nakujaproject/Internship-2026/03_RECOVERY/Weekly_Memo/Recovery Week 2 Report .pdf

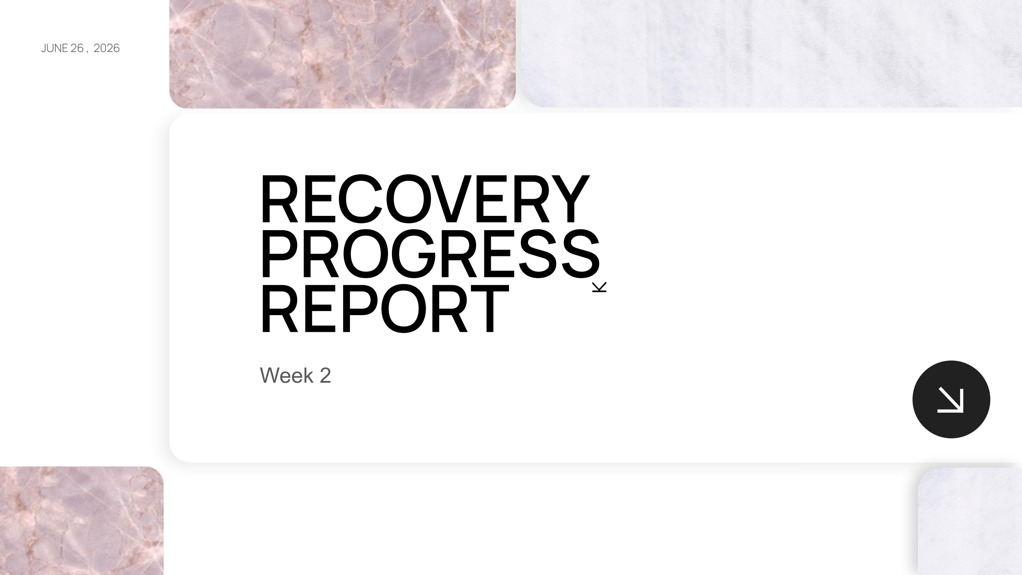
[picture p94: page 1]

K

# RECOVERY PROGRESS REPORT

## Week 2

JUNE 26 , 2026

# This Week’s Tasks

## - - XBEE Antenna Research - - General purchases and beginning of X-BEE importation process - -Free RTOS Configuration Review - - 3D printing Shear Pins - - Implement circuit changes for dual memory storage - - Documentation - - Code cleaning - - cooking crimson powder

# Extracting data from the flash memory

## 1. Fixing the flash memory erase

The initial software attempted to clear the SPI flash memory using a standard byte-overwrite method. This was ineffective because NOR flash hardware strictly requires a dedicated sector-erase command to reset memory bits and prevent data corruption.

## 2. Reading the data correctly

The recovery program was trying to read complex binary code from a file named 'flight', while the flight computer was actually saving simple plain text into a file named 'data'.

The flight computer was saving the telemetry data as simple, plain text . But the recovery program was trying to read it as complex binary code. Because of that mismatch, the recovered data just looked like gibberish.

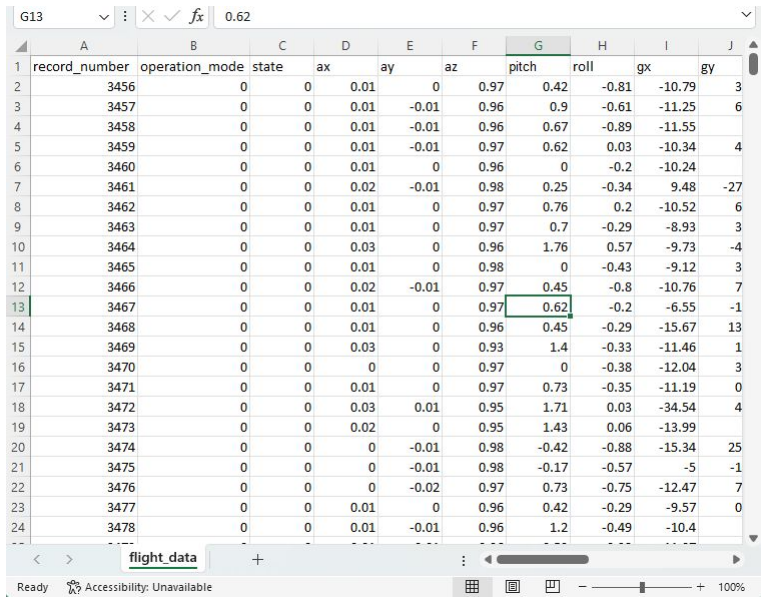
[picture p95: figure]

## 1. Successfully extracted the sensor data from the Flight Computer (FC) 2. Validation will be conducted accordingly 3. GPS not connected - TBD

# Updated the base station schematic and designed the PCB

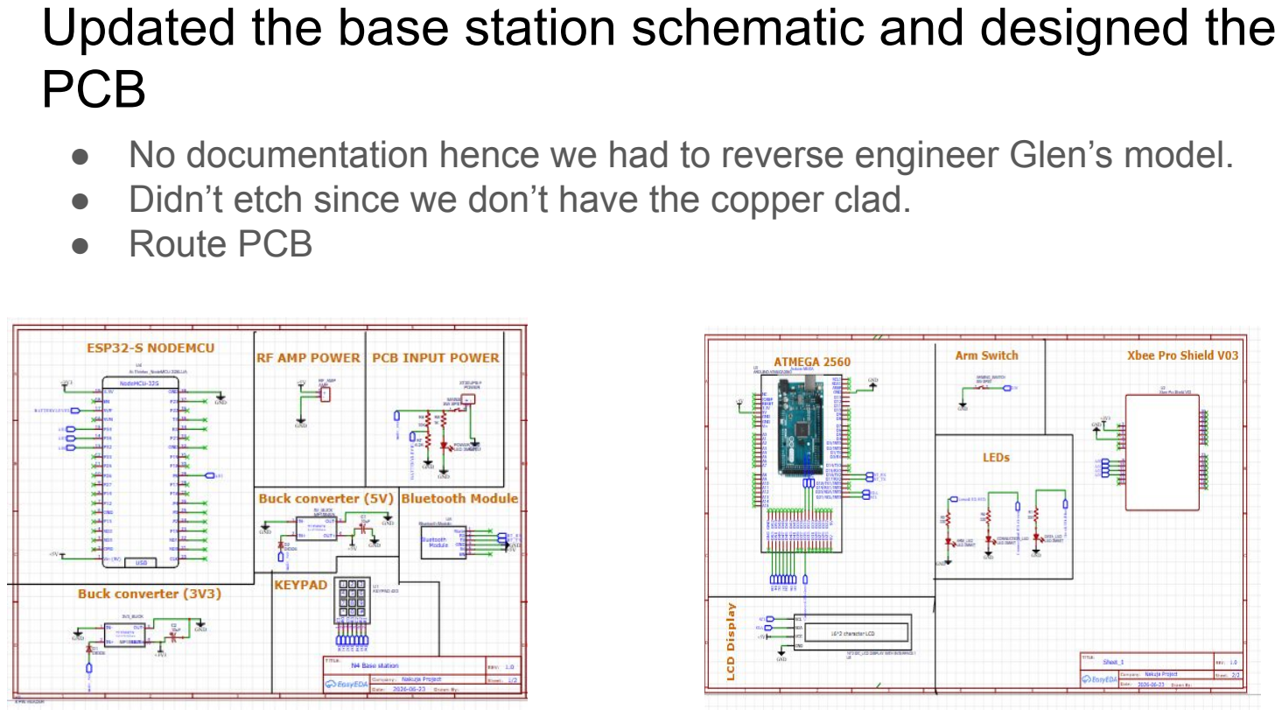
[picture p96: page 5]

- No documentation hence we had to reverse engineer Glen’s model.
- Didn’t etch since we don’t have the copper clad.

## - Route PCB

# Routed PCB

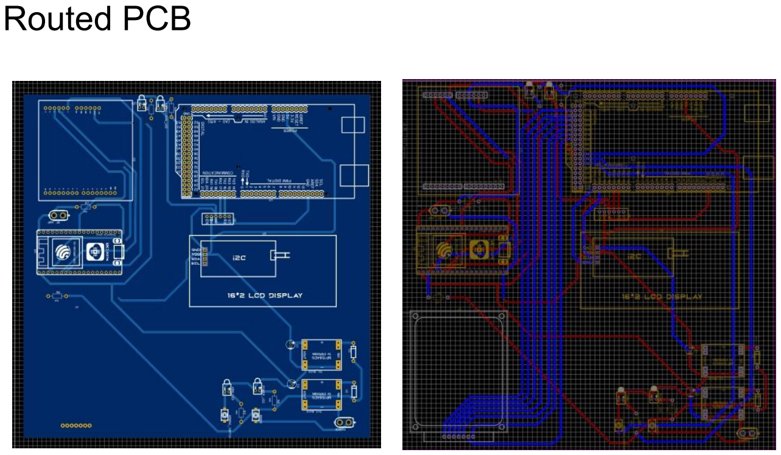
[picture p97: page 6]

# Designed Battery Holder for Base Station

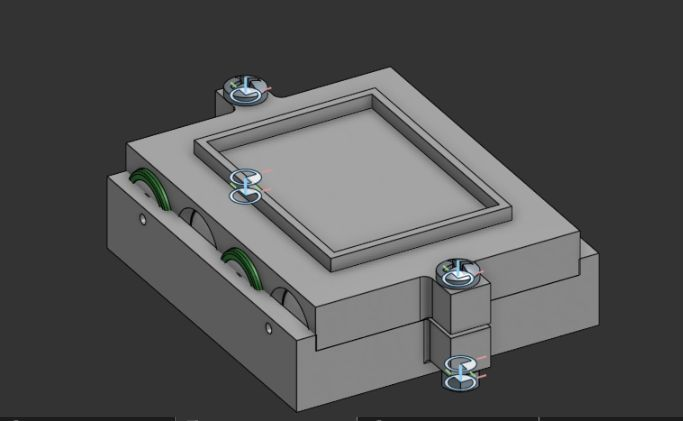
[picture p98: figure]

Is yet to be 3D printed.

# Code Review and Cleaning

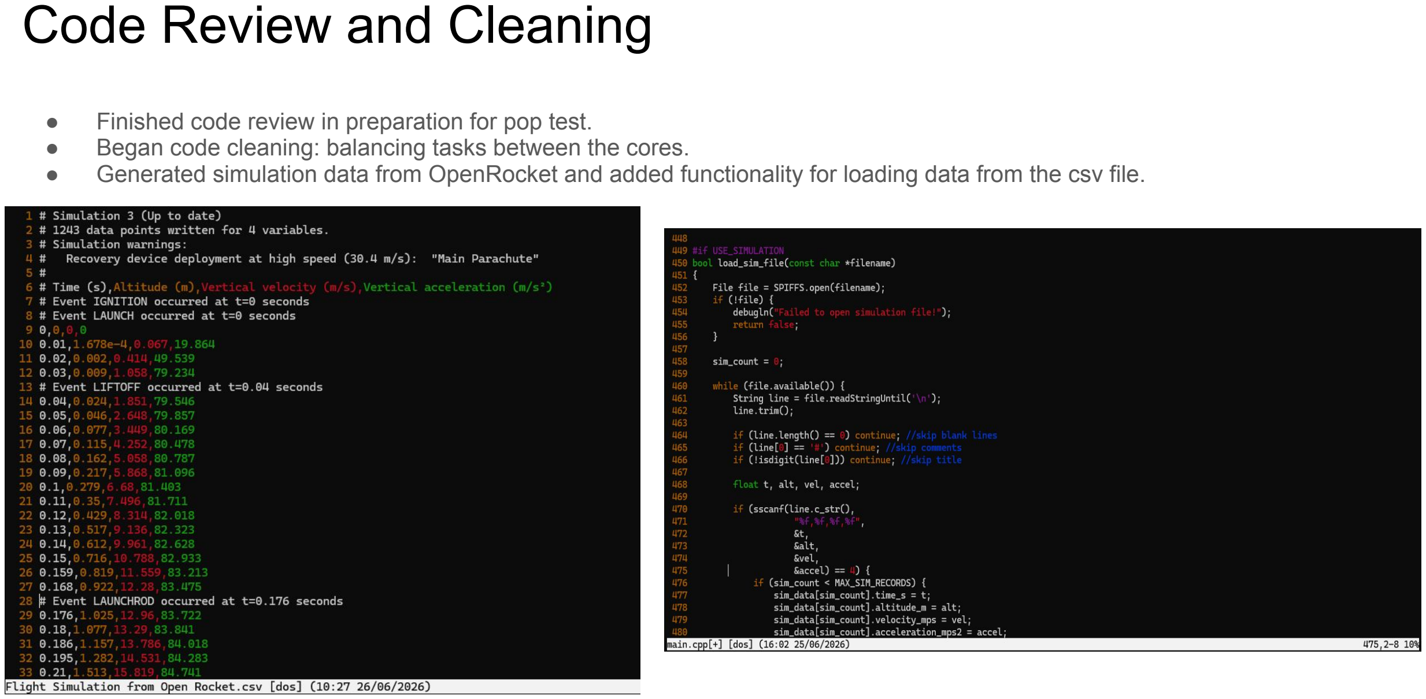
[picture p99: page 8]

- Finished code review in preparation for pop test.
- Began code cleaning: balancing tasks between the cores.
- Generated simulation data from OpenRocket and added functionality for loading data from the csv file.

# Dockerized the Base Station

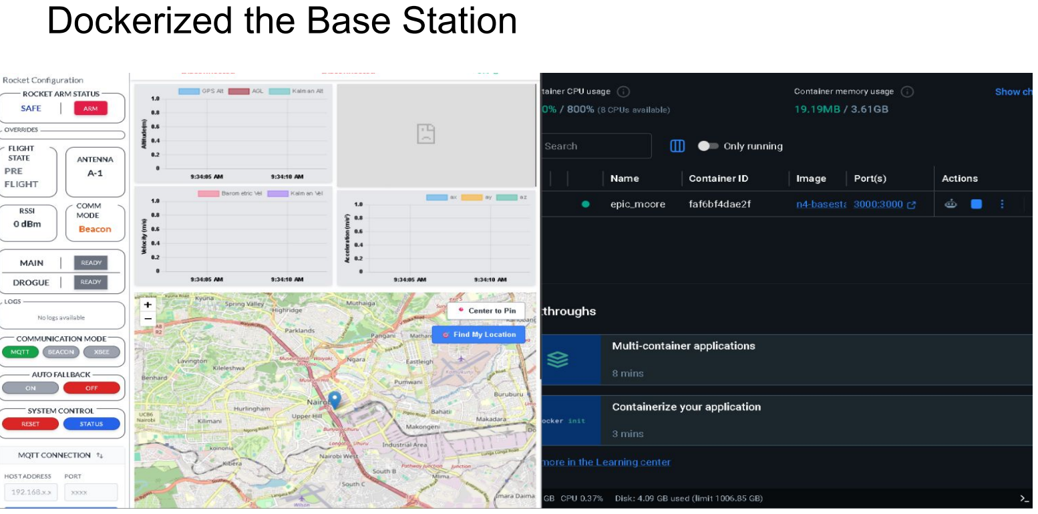
[picture p100: page 9]

# Use of COTS altimeter as backup

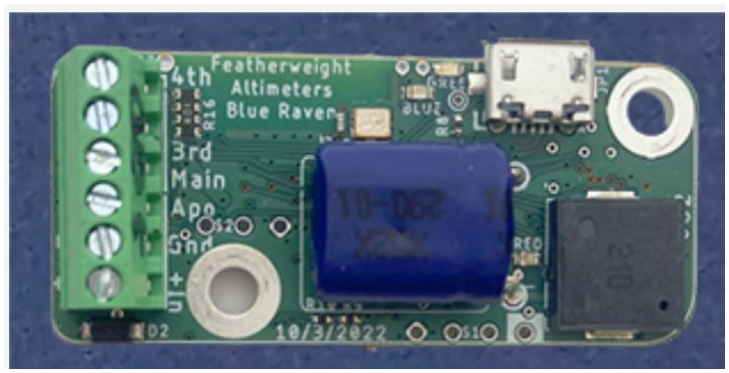
[picture p101: figure]

### https://www.apogeerockets.com/Electronics-Payloads/Dual-Deploy ment/Blue-Raven-Altimeter

# Next weeks tasks

- Etch Base-Station PCB - Pop test - 3D - Printing shear pins ,Battery Holder, explosion caps - Kalman Filter Testing - Make circuit changes for dual memory storage - Verification of parachute design to ensure they are able to handle the new motor etc - Changes to base-station Arduino MEGA code - Extending parachute suspension lines
