nakujaproject/Internship-2026/03_RECOVERY/Weekly_Memo/RECOVERY PROGRESS REPORT WEEK 1.pdf

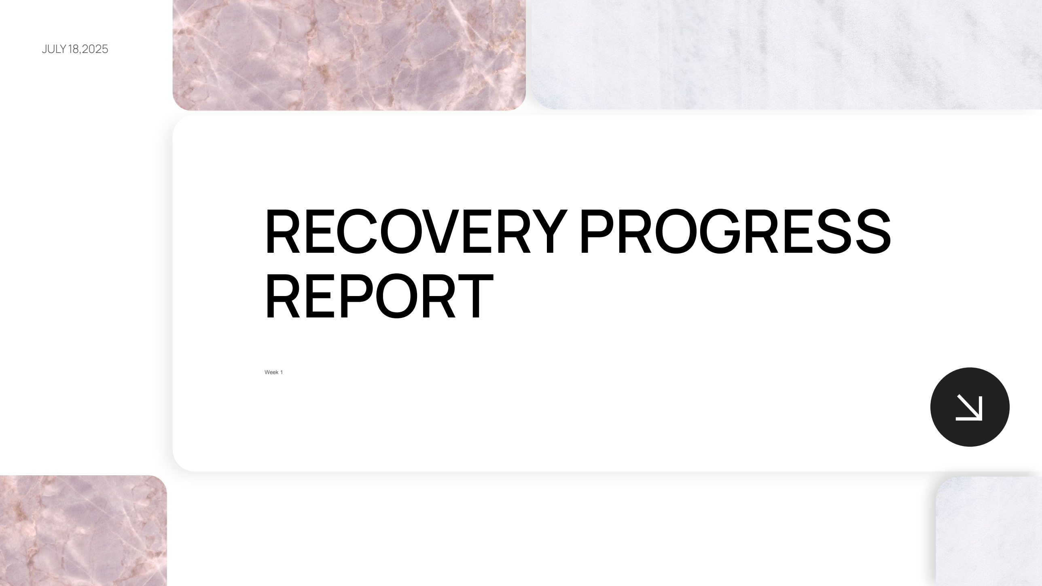
[picture p102: page 1]

# RECOVERY PROGRESS REPORT

Week 1

JULY 18,2025

# This Week’s Tasks

Define tasks for 12 weeks and develop mind map for doing them Set up base-station on every PC
Connect Base Station to Flight Computer
Brief on Parachute System by Mwaura based on his project Brief by Glenn based on his project
Explanation of Kalman Filter Implementation
Inventory

## Defining the 12 weeks tasks and Developing a Mind Map

Github Projects

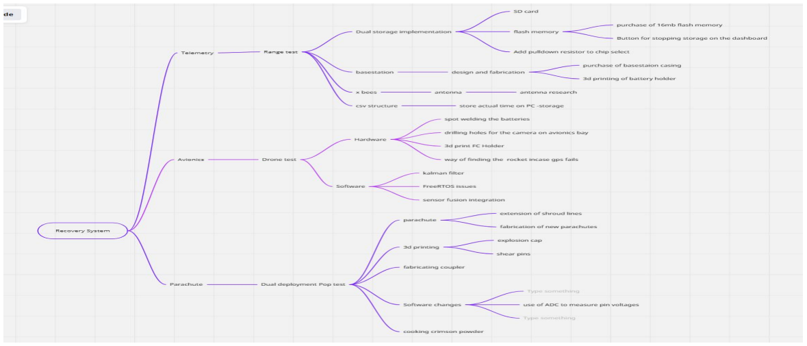
[picture p103: figure]

## Setting Up Base Station on Every PC

Changes made for cross platform compatibility

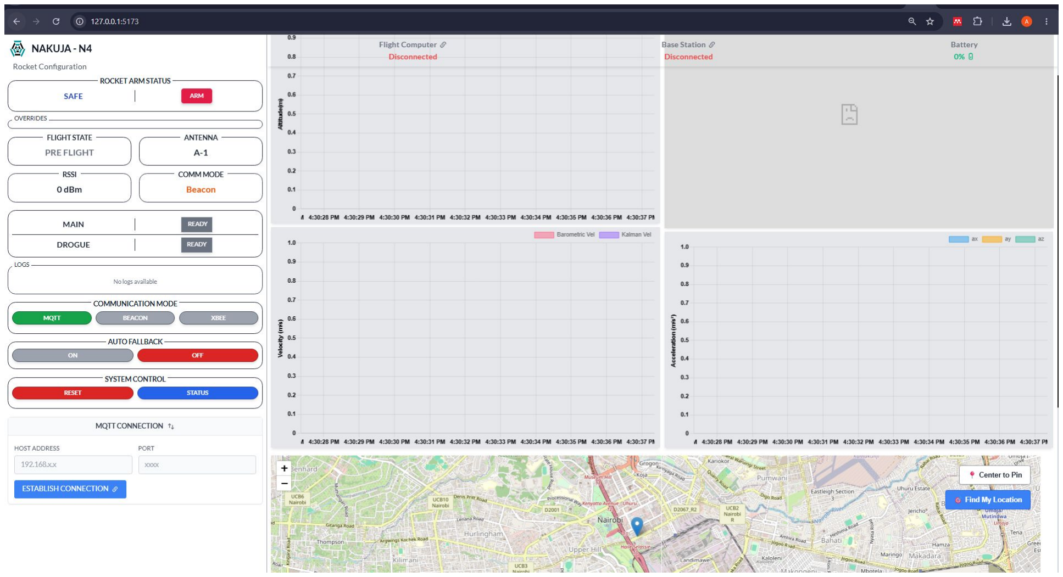
[picture p104: figure]

## Pop Test DRY RUN

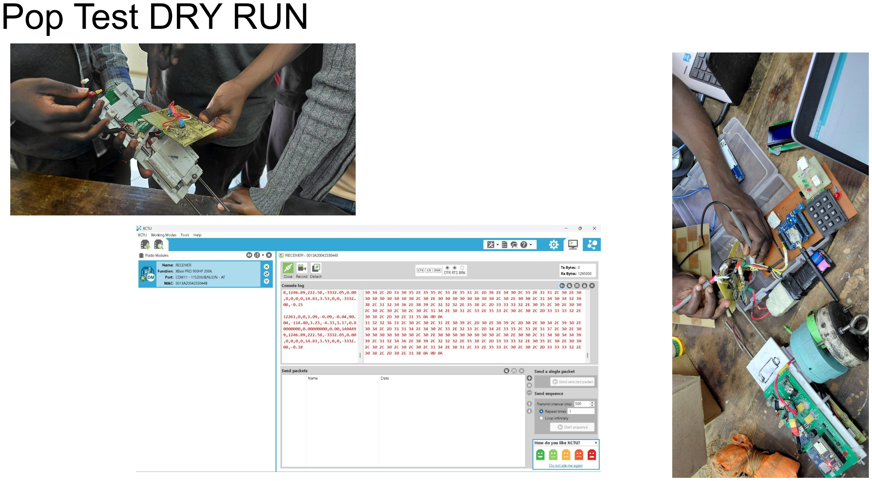
[picture p105: page 5]

# Next Week’s task

- XBEE Antenna Research
- General purchases and beginning of X-BEE importation process
- Machining Coupler
-Free RTOS Configuration Review
- 3D printing Shear Pins
- Research on the effects of pressure changes in the avionics bay during flight
- Implement circuit changes for dual memory storage
- Documentation
- Code cleaning
