nakujaproject/Internship-2026/02_AIRFRAME/Weekly_Memo/Airframe week two progress report.pdf

# Airframe team

Week two Progress Report

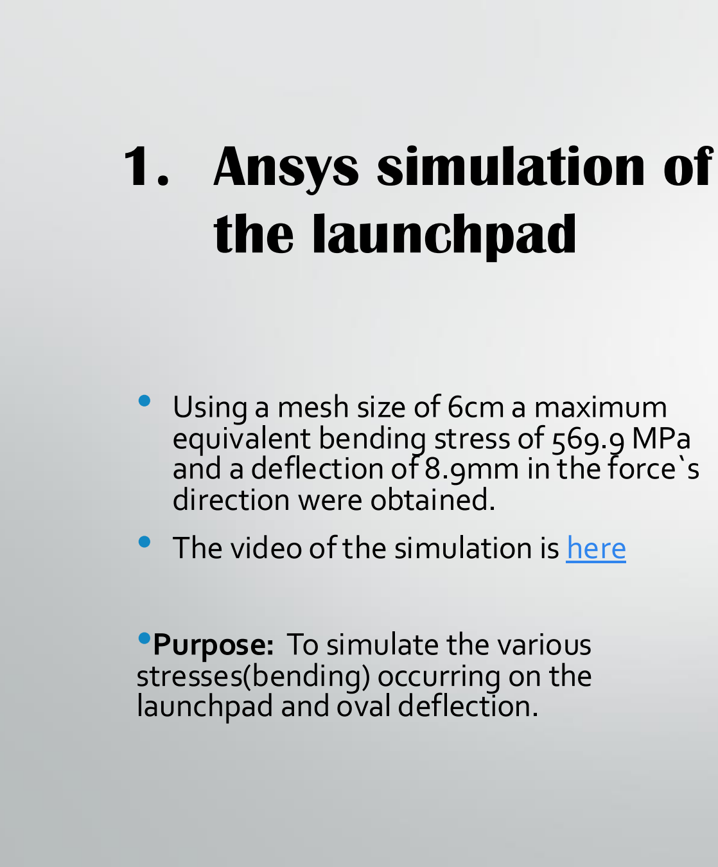
[picture p106: figure]
1. Ansys simulation of the launchpad; • Using a mesh size of 6cm a maximum equivalent bending stress of 569.9 MPa; direction were obtained. • The video of the simulation is here; •Purpose: To simulate the various stresses(bending) occurring on the launchpad and oval deflection.
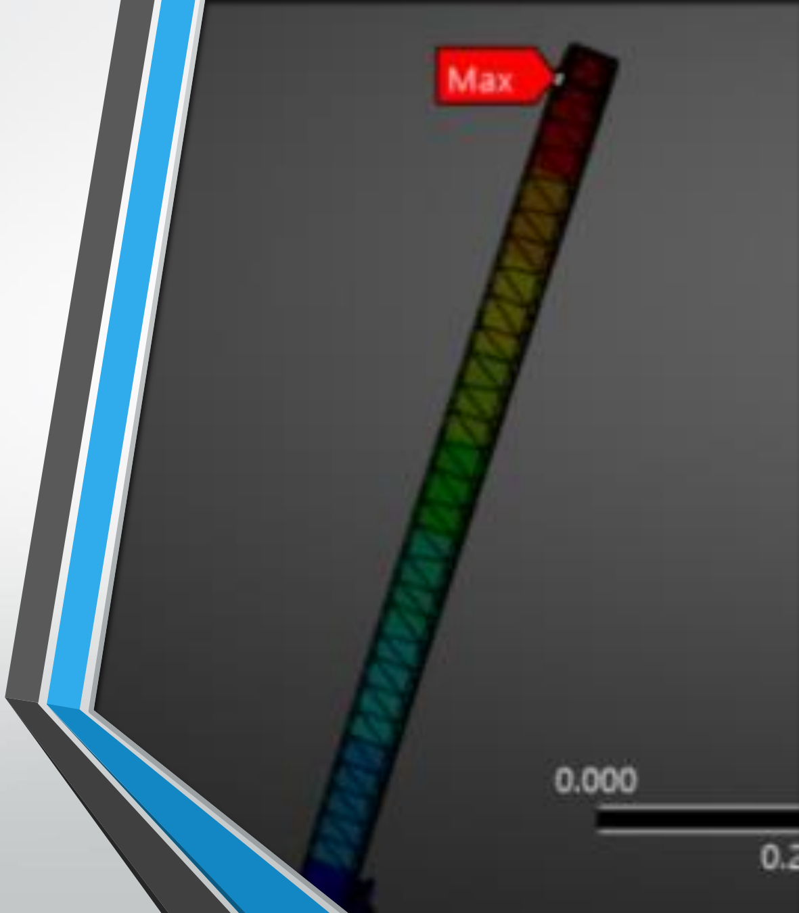
[picture p107: figure]

and a deflection of 8.9mm in the force`s

## 2.Mesh independence study of the launchpad

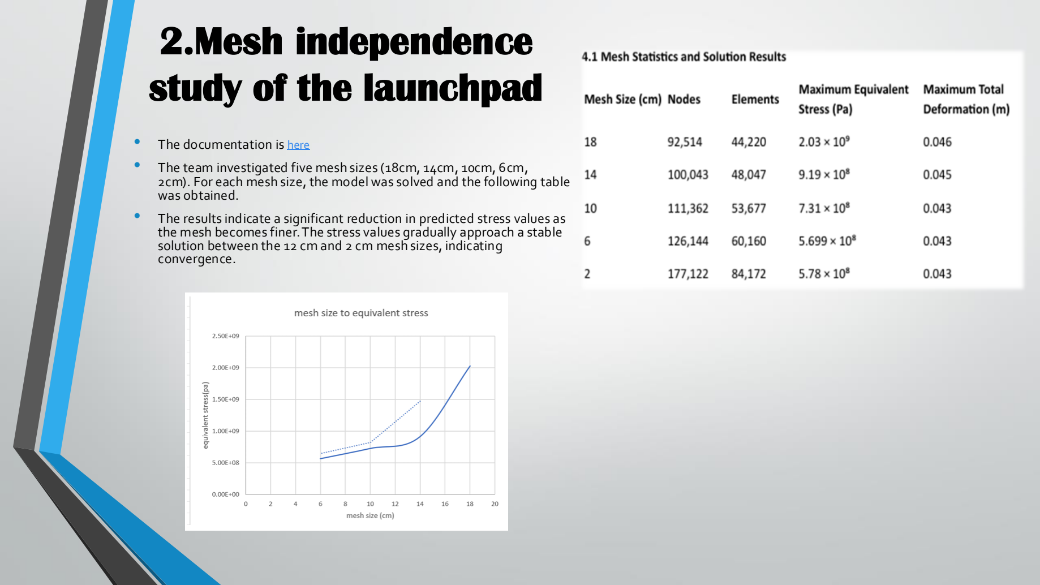
[picture p108: page 3]

- The documentation is here (https://discord.com/channels/1062703976711209010/1062705386697801828/1519920103523618966)
- The team investigated five mesh sizes (18cm, 14cm, 10cm, 6cm, 2cm). For each mesh size, the model was solved and the following table was obtained.
- The results indicate a significant reduction in predicted stress values as the mesh becomes finer. The stress values gradually approach a stable solution between the 12 cm and 2 cm mesh sizes, indicating convergence.

- For deformation, the results remain nearly constant throughout the refinement process, demonstrating that deformation predictions are largely insensitive to further mesh refinement beyond the 6 cm mesh.

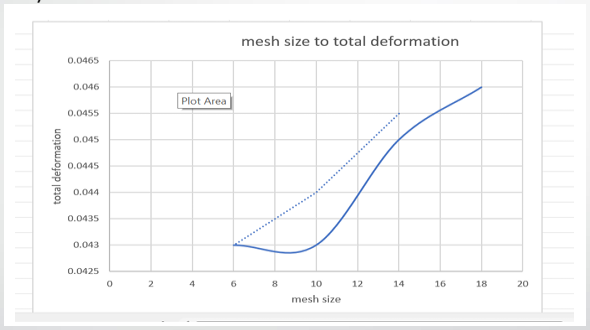
[picture p109: figure]

- Based on the convergence behavior observed during mesh refinement, the 6 cm mesh was selected for all subsequent analyses s because it provides accurate results while minimizing computational requirements.

## 3. Theoretical calculations of stress(

bending and axial), deflection,

## buckling analysis and safety of factor

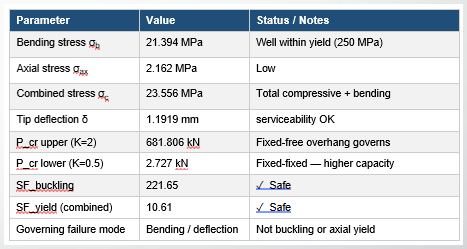
[picture p110: figure]

- The team embarked on the theoretical analysis of the launchpad to verify the ansys simulations.
- The documentation is here (https://discord.com/channels/1062703976711209010/1062705386697801828/1519937529242058773) and the following results were obtained:
- The deflection obtained is almost similar to the ansys simulation (0.78 of the simulation). The stresses can`t be directly compared as he theoretical is directional while the simulation is equivalent.

## 4. Airframe Tasks preparation and listing

- The team was also able to prepare a mindmap of all the tasks that
need to be undertaken here (https://app.xmind.com/share/8dNVX2TA?xid=Qb3cZIfH)

## 5. Challenges experienced

- Lack of internet connection.
- Lack of access to workshops for fabrication.
- Computational resources required for Ansys.

Next week tasks
- Launchpad finishes: reaming, painting etc

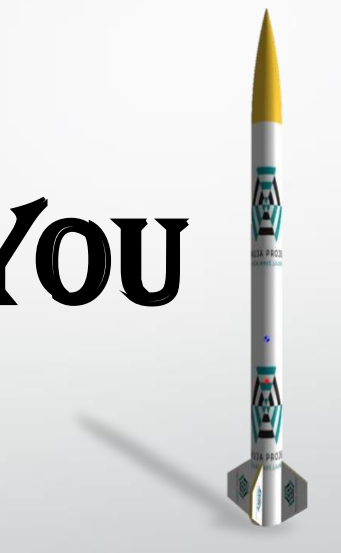
[picture p111: figure]

# Thank you
