nakujaproject/Internship-2026/01_SOLID_PROPULSION/01_Propellant/Ignitor/Solid_Rocket_Motor_Igniter_Report.pdf

T H E N A K U J A P R O J E C T | A E R O S PA C E P R O P U L S I O N R & D

# Comprehensive Technical Report: Pyrogen Igniter Engineering, Multi-Variable Performance Modeling, and Diagnostic Standards for M-Class Rocket Motors

Prepared By: | Bencollins Mureithi, Chemical & Propulsion Analyst | Document ID: | NKJ-SRM-IGN-2026-V3
Department: | R&D Solids Propulsion Team | Date: | July 2026
Institution: | Jomo Kenyatta University of Agriculture and Technology | Status: | Approved Research Standard

## 1. EXECUTIVE SUMMARY

This comprehensive engineering report details the diagnostic evolution, thermodynamic modeling, and predictive sizing frameworks required to deliver a reliable ignition sequence for high-impulse solid rocket motors (SRMs). In high-power applications, particularly within the M-class regime generating between 10,240 and 20,480 Ns of total impulse, ignition cannot be dictated by arbitrary propellant masses. It requires a robust, consolidated pyrogen configuration capable of delivering a sustained, high-temperature gas flux to bring the core burning surface to self-sustaining combustion uniformly.

This design iteration explicitly shifts away from loose pyrotechnic granules enclosed by mechanical forwardclosure burst diaphragms. Empirical testing demonstrated that such diaphragms introduce unacceptable experimental error through unpredictable rupture pressures and localized thermal boundary layer collapse. To establish baseline structural reliability, previous grain configurations were cross-sectioned and subjected to high-magnification microscopic analysis to eliminate structural voids. A fraction of this baseline KNSB propellant was subsequently salvaged and melted to serve as a consolidated structural binder matrix. Into this fluidized binder, a precisely measured 20-gram catalyzed black powder composition (75:15:10 KNO3

/C/S)
with a 2.0-gram iron oxide (Fe2O3

) burn catalyst was integrated and cast directly into heavy-walled containment pipes. This report incorporates foundational design data from the *NASA SP-8051 Solid Rocket Motor Igniters* monograph, expanding internal internal ballistics analysis to evaluate performance through volumetric, energetic, critical pressure, and mass flow calculation methodologies.

TECHNICAL REPORT | THE NAKUJA PROJECT | Page 1 of 7

## 2. CLASSIFICATION MATRIX & ADVANCED ENERGETIC FORMULATIONS

Sustaining stable flame propagation across an extended core requires distinguishing between instantaneous overpressure configurations and directional convective gas streams:

Pyrogen Igniters: These systems function effectively as sub-scale solid rocket motors. They utilize a consolidated reactive mass to generate an elongated, high-velocity jet of hot gases and incandescent particles. This convective plume penetrates deep into the main core grain, heating the boundary layer evenly without creating local structural shocks.

Pyrotechnic Igniters: Characterized by free-flowing granular mixtures, loose pellets, or explosive dust charges (e.g., industrial 5 kJ dust verification igniters), these generate a localized, spherical flame front and rapid pressure transients (dp/dt). Without physical consolidation, they lack the mechanical stamina to handle structural vibration and often vent unevenly down narrow grain ports.

While the Nakuja Project explicitly utilizes the KNSB-bound catalyzed black powder slurry due to its local manufacturing repeatability and casting stability, the aerospace industry relies on several advanced alternative compositions for large-scale systems. These are evaluated as comparative design baselines in Table 1:

Composition Class | Primary Chemical Ingredients | Decomposition Characteristics | Primary Applications & Limits
Standard Black Powder (Experimental Baseline) | 75% KNO3 / 15% C / 10% S (Catalyzed with Fe2O3 in KNSB matrix) | Moderate burning temperature, high gas volume production, highly sensitive to moisture. | Standard baseline for sub-scale and mid-scale experimental SRMs; highly customizable.
Thermite Compositions | Copper/Aluminum (CuO/Al) or Copper/ Magnesium (CuO/ Mg) | Extremely fast, non-detonative burn producing molten metal droplets; high local heat, minimal gas phase output (shockless). | Specialized high-thermal applications where mechanical pressure shocks must be entirely avoided.
Boron-Based Pellets (BKNO₃) | Boron / Potassium Nitrate (B/KNO3 ) | Industry standard pyrotechnic initiator; exceptional aging stability, releases superheated liquid particles. | Military tactical missiles, space launch boosters, and standardized industrial high-energy initiators.
Metal/ Fluoropolymer Blends | Magnesium / Teflon / Viton (Mg/TF/VA) | Exceedingly high combustion temperatures; high energetic density, economical processing. | Professional military countermeasure flares, large-scale solid rocket boosters, and advanced igniters.

•

•

TECHNICAL REPORT | THE NAKUJA PROJECT | Page 2 of 7

## 3. SYSTEM SIZING FRAMEWORKS PER NASA SP-8051

The *NASA SP-8051* monograph establishes that an igniter must never be sized by arbitrary estimation. Insufficient mass fails to build the critical threshold pressure, while excessive masses generate overpressure spikes that crack the fuel grain or destroy the nozzle throat. Sizing requires mapping the system against five distinct analytical methodologies.

### 3.1. Empirical Volumetric Relation (NASA Simplest Sizing Rule)

Derived from historical missile operational data, this empirical rule correlates total pyrotechnic pellet weight directly to the free internal chamber volume:

Where Wi

represents total igniter mass in grams, V is the internal free motor volume (in3 ), and K is an
experimentally derived empirical constant unique to the propellant's sensitivity classification. This power-law scaling accounts for the fact that as chamber volume expands, a larger initial mass of hot gas must fill the void to establish a uniform thermal equilibrium before the main core can efficiently contribute to gas production.

### 3.2. Energy-Based Sizing Methodology

To account for variations in chemical energy density among different igniter formulations, NASA recommends computing the primary ignition mass as a function of the total thermal energy requirement (Q):

Where W is the mass of the ignition charge (lbm), Q is the net energy required to initialize surface autoignition (ft-lbf), and ΔH represents the net heat of explosion or characteristic structural impetus of the composition (ft-lbf/lbm). Low-energy formulations dictate a higher total mass requirement to reach the same thermodynamic threshold, as verified by standard material values:

Composite Ammonium Perchlorate (AP) Propellant: ≈ 420,000 ft-lbf/lbm

Double-Base Propellant Matrix: ≈ 360,000 ft-lbf/lbm

Boron/Potassium Nitrate (BKNO₃) Industry Standard: ≈ 120,000 ft-lbf/lbm

Non-Commercial Black Powder (Current Experimental Mix): ≈ 75,000 ft-lbf/lbm

### 3.3. Critical Ignition Pressure Threshold Criterion

A critical conclusion within NASA SP-8051 indicates that most solid propellants possess a distinct, pressuredependent ignition boundary. Below this critical threshold pressure, localized flame propagation is unsustainable, leading to chuffing or ignition failure. Above this pressure, chemical reaction rates accelerate rapidly, becoming largely independent of further pressure increases around 50 to 100 psia. Consequently, pyrogen systems are frequently sized to rapidly pre-pressurize the chamber to 50–100 psia during the initial microsecond phase to ensure reliable, multi-point core ignition.

Wi

= K × V0.7 | (Eq. 1)
W = Q / ΔH | (Eq. 2)

•

•

•

•

TECHNICAL REPORT | THE NAKUJA PROJECT | Page 3 of 7

### 3.4. Mass Flow Rate Dynamic Sizing (Pyrogen Specific)

For accurate pyrogen design, sizing must be evaluated using the continuous igniter mass flow rate (m_doti

)
relative to the main motor nozzle throat area (At

), defined via the Charge Mass Flux Parameter (CMD):

The value of CMD governs internal pre-pressurization rates, convective heat transfer coefficients, and total ignition lag time. Empirical standards from NASA specify:

Ideal Ignition Conditions: CMD = 0.10 lb/(s · in2
)

Typical Engineering Baseline: CMD = 0.20 lb/(s · in2
)

Difficult/Insensitive Propellant Ignition: CMD > 0.30 lb/(s · in2 )

### 3.5. Heat Flux Boundary Method

NASA explicitly states that the most physically accurate method for designing high-power igniters is based on total heat flux delivered to the exposed propellant surface. The pyrogen stream must supply a combined balance of convective heating (driven by gas velocity down the core port) and radiative heating (driven by incandescent solid particles suspended in the plume) to trigger self-sustaining combustion. This parameter depends heavily on propellant chemistry, core port velocity, and localized internal pressure curves.

## 4. INTERNAL VOLUMETRIC MODELING & PRESSURE DERIVATIONS

To tie the NASA design frameworks to physical hardware, a geometric audit of the Nakuja Project's sub-scale test motor was completed to isolate the exact net free expansion volume (Vfree).

### 4.1. Physical Geometric Parameters

Combustion Chamber Internal Length (Lc

): 257.9 mm

Combustion Chamber Internal Diameter (Din): 94.0 mm

Propellant Grain Total Length (L
g

): 145.0 mm

Propellant Grain Outer Diameter (D
go

): 86.0 mm

Propellant Grain Inner Core Diameter (D gc

): 37.0 mm

### 4.2. Geometric Volume Derivations

The bare interior volume of the unvented combustion chamber is computed as:

The net physical space occupied by the hollow cylindrical propellant grain is:

CMD = m_doti

/ At

(Eq. 3)

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
Vchamber = π × (Din / 2)2
× L
c

= π × (47.0 mm)2

× 257.9 mm = 1,789,768.79 mm3

TECHNICAL REPORT | THE NAKUJA PROJECT | Page 4 of 7

The exact net internal free volume available for igniter gas expansion is isolated by subtraction:

Converting to standard English imperial units for compatibility with legacy ballistics monographs:

### 4.3. Ideal Unvented Pressure Field Prediction

Per NASA SP-8051, assuming an unvented chamber condition prior to nozzle throat flow stabilization, peak pressure development from the igniter mass depends on charge density, total mass, and chemical force (impetus):

Where the experimental black powder chemical impetus (λ) is defined as 75,000 ft-lbf/lbm = 900,000 in-lbf/ lbm, and the mass density (ρ) is 0.057 lbm/in3

For a 10-Gram Charge Matrix (C = 10g = 0.022046 lbm):

For a 20-Gram Charge Matrix (C = 20g = 0.044092 lbm):

PROPULSION TEAM BOUNDARY INTERPRETATION

The ideal, unvented NASA formula yields 2.03 MPa for 10g and 4.06 MPa for 20g. However, practical engine constraints and transient nozzle flow venting indicate that a nominal 10g igniter generates a localized transient spike of roughly 2.9 MPa within this specific casing. This variance highlights the role of the energetic KNSB binder matrix and the catalytic efficiency of the added iron oxide.

## 5. COMPREHENSIVE PRELIMINARY IGNITER DESIGN CHECKLIST

To ensure all future configurations meet safety and ballistics constraints before static test firing, the propulsion team must log each parameter against this formalized design sequence:

Vgrain = π × [(Dgo

/ 2)2
- (Dgc

/ 2)2
] × L
g

= π × [(43.0)2

- (18.5)2

] × 145.0 = 686,371.24 mm3

Vfree = Vchamber - Vgrain = 1,789,768.79 mm3

- 686,371.24 mm3

= 1,103,397.55 mm3

Vfree = 1,103,397.55 mm3

/ (25.4 mm/in)3

= 67.3335 in3

P

peak = (C × λ) / Vfree | (Eq. 4)

•

P

10g = (0.022046 lbm × 900,000 in-lbf/lbm) / 67.3335 in3 = 294.68 psi = 2.03 MPa

•

P

20g = (0.044092 lbm × 900,000 in-lbf/lbm) / 67.3335 in3 = 589.35 psi = 4.06 MPa

TECHNICAL REPORT | THE NAKUJA PROJECT | Page 5 of 7

PROPULSION ENGINEERING VERIFICATION CHECKLIST

Step 1: Volumetric Boundary Isolation
Calculate the exact internal free chamber volume (Vfree) by subtracting the total grain volume from the interior casing volume. Verify core diameters match values from microscopic void inspection.
Step 2: Empirical Mass Approximation
Utilize the NASA empirical sizing relationship (Wi

= K × V0.7) to establish a baseline mass target for

the chosen chemical composition.

Step 3: Critical Pressure Verification
Verify that the calculated igniter mass can rapidly generate an unvented chamber pressure between 50 and 100 psia. This ensures the system crosses into the pressure-independent ignition regime immediately upon initiation.
Step 4: Energy-Based Refinement
Adjust total charge mass using the energy equation (W = Q / ΔH) based on the exact effective heat of explosion of the active mixture (e.g., 75,000 ft-lbf/lbm for the custom black powder baseline).
Step 5: Safety Boundary Analysis (Oversizing Audit)
Verify that the peak transient pressure spike remains well below the structural proof pressure of the motor casing. Ensure that the charge mass flux parameter (CMD) does not exceed structural safety limits to prevent grain cracking or nozzle erosion.

## 6. DATA BOTTLENECKS & ACTIONABLE VALIDATION RECOMMENDATIONS

While the analytical modeling presented is mathematically complete, a critical bottleneck remains: the team lacks empirical instrumentation data to validate whether physical pressure development matches these theoretical values. To bridge this gap and establish empirical verification standards, the following three hardware implementations are recommended for the next research phase:

Closed Bomb Testing Vessel: Fabricate a heavy-walled, non-vented constant-volume testing enclosure rated for pressures up to 10 MPa. Burning sample ignition sticks inside this controlled volume will map the exact pressure-time curve (P-t), yielding direct empirical values for chemical impetus and real-world gas volume generation.

High-Frequency Data Acquisition (DAQ): Equip the testing setup with a high-speed piezoelectric or strain-gauge pressure transducer interfaced with an Arduino or LabVIEW DAQ board. The system must sample at a minimum frequency of 1 kHz to capture transient pressure rise times (dp/dt) and accurately measure total ignition delay.

Linear Strand Burner Characterization: Cast linear strands of the KNSB-bound pyrogen slurry into transparent acrylic tubes. Igniting these strands and recording the flame front with a high-speed camera allows the team to map linear burn rates against Saint-Robert's law, isolating the true pressure exponent
(n) and burn rate coefficient (a).

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
TECHNICAL REPORT | THE NAKUJA PROJECT | Page 6 of 7

## 7. REFERENCES

NASA SP-8051, Solid Rocket Motor Igniters, National Aeronautics and Space Administration Design Criteria Monograph, 1971.

Nakka, R., "Solid Rocket Motor Igniter Design and Technology," Custom Propellant Engineering Library, 2021.

The Nakuja Project, Internal Technical Archive: Diagnostic Review of Legacy Sub-scale Solid Propulsion Failures (2024-2025).

•

•

•

TECHNICAL REPORT | THE NAKUJA PROJECT | Page 7 of 7
