nakujaproject/Internship-2026/01_SOLID_PROPULSION/01_Propellant/Grains/Technical_Report_On_Mitigation_Of_Pressure_Spikes.pdf

## TECHNICAL REPORT: MITIGATION OF UNPREDICTABLE PRESSURE SPIKES IN BATES

Prepared by: Bencollins Mureithi Team: The Nakuja Project
June 16, 2026

### 1. Introducon

- Background:

Experimental rocketry requires high ballisc consistency for safety and performance. The BATES (Ballisc Test and Evaluaon System) grain geometry is specifically engineered to provide a neutral, stable thrust profile through a maintained burning surface area. However, praconers oen observe errac, non-neutral pressure-me curves characterized by sudden spikes and deviaons from simulaon. These phenomena indicate that the propellant is not burning according to its geometric design.
- Objecves:

This research aims to address these performance instabilies by ensuring grain structural integrity and achieving predictable combuson kinecs through the opmizaon of the propellant matrix and ignion systems.

### 2. Technical Discussion

The transion from errac pressure spikes to predictable combuson requires managing both the physical state of the grain and the dynamics of the ignion process.

### 2.1 Rheological and Structural Integrity

The formaon of voids and micro-cracks is the primary driver of unpredicted pressure surges.
- Surfactant Integraon: Molten sorbitol exhibits high surface tension, which can hinder the weng of KNO3 parcles and lead to air entrapment. The addion of surfactants, such as Sodium Laureth Sulfate (SLES) or Lecithin, serves to reduce this interfacial tension. This promotes a homogeneous, void-free slurry that ensures the grain burns uniformly without localized hot spots.

- Plascizaon: Sorbitol inherently forms a brile, crystalline matrix that is suscepble to thermal shock and mechanical fracture. Incorporang plascizers like glycerol introduces flexibility into the binder, allowing the grain to resist crack propagaon under operang pressures. By maintaining a crack-free structure, the propellant preserves its intended burning surface area.

### 2.2 Combuson Kinecs and Ignion

Controlling the burn rate involves moderang both the thermal output and the chemical iniaon.
- O/F Rao and Parcle Size: Shiing the Oxidizer-to-Fuel rao from the standard 65:35 toward a 60:40 or 58:42 composion increases the fuel-rich binder content, which acts as a thermal heat sink to moderate peak combuson temperatures. Simultaneously, using coarser KNO3 parcles prolongs the melng phase, resulng in a more controlled, gradual release of oxygen.
- Ignion Reliability: Delayed ignion contributes to non-uniform pressure rises. Implemenng a two-part ignion system—consisng of a high-sensivity primer and an internal pyrogen charge—ensures that the enre grain surface iniates combuson simultaneously, prevenng the localized pressure surges associated with slow or uneven ignion.

### 3. Ignion System Design: Raonale and Diagnosc Criteria

The propulsion system employs a two-part ignion sequence consisng of an iniator (igniter) and a surface-applied propellant primer. This configuraon is crical for achieving reliable, synchronized ignion across the grain surface and migang the risks associated with transient ignion delays.

### 3.1 Necessity of the Two-Part System

The requirement for a dual-stage system arises from the physical and chemical properes of the solid propellant grain, which oen possesses high auto-ignion temperatures or geometries that challenge uniform flame propagaon.
- Sensivity Bridging: The primer serves as an intermediary layer with high sensivity to thermal flux. The igniter provides the inial high-energy output required to trigger the primer, which in turn acts as a high-intensity catalyst to force the main propellant grain into self-sustaining combuson.
- Simultaneous Flame Propagaon: Reliance on a single igniter can result in localized ignion, leading to uneven burning or combuson instabilies. The primer ensures the flame front spreads instantaneously across the enre exposed propellant surface area, facilitang a rapid and controlled pressure rise to design levels.
- Migaon of Hang-Fire: The system design proacvely prevents "hang-fire" scenarios— where ignion is delayed beyond the specified me window—by ensuring that energy transmission is uniform and effecve across the combuson chamber.

### 3.3 Diagnosc Idenficaon of Delayed Ignion

Indicator | Characterisc Behaviour | Interpretaon
P-t Slope | A disnct "step" or "plateau" in the pressure curve immediately following the acvaon signal | Indicates a lag between the inial igniter discharge and the onset of stable grain combuson.
Ignion Interval | Time duraon from the electrical acvaon signal (t0) to the achievement of 10% of maximum chamber pressure (Pmax). | Exceeding the design-specified threshold for this interval constutes a confirmed ignion delay.
Acousc/Vibraon Data | Sharp, irregular pressure spikes or "chuffing" sounds | Suggests non-uniform flame propagaon or the accumulaon of gases before sudden, violent ignion of the grain.

Monitoring these parameters ensures that the transion from inial ignion to steady-state interior balliscs remains within established safety and performance envelopes.

### 4. Conclusion

The errac ballisc performance observed in BATES-configured KNSB motors is largely a result of structural defects and inconsistent iniaon dynamics. By focusing on grain structural integrity—specifically through the use of surfactants to eliminate voids and plascizers to prevent fractures—and refining combuson kinecs via O/F rao adjustments and improved ignion, the motor's actual chamber pressure can be aligned with simulated design predicons

### 5. References

- Nakka, R. (n.d.). "KN-Sorbitol Propellant." Richard Nakka's Experimental Rocketry Web Site.
- European Conference for Aeronaucs and Space Sciences (EUCASS). (2019). "Laser Ignion and Combuson Study of KNO3-Sorbitol based Solid Propellant".
- Technical Report: "Surfactants & Plascizers for KNSB Solid Propellant" (The Nakuja Project, 2026).
