nakujaproject/Internship-2026/01_SOLID_PROPULSION/01_Propellant/Ignitor/Comprehensive_Nichrome_Igniter_Analysis.pdf

T H E N A K U J A P R O J E C T | A E R O S PA C E P R O P U L S I O N R & D

# Comprehensive Technical Report: Mathematical Modeling and Sizing Constraints of Nichrome 80 Conductor Elements for Pyrogen Systems

Prepared By: | Bencollins Mureithi, Chemical & Propulsion Analyst | Document ID: | NKJ-PROP-EE-2026-V2
Department: | R&D Solids Propulsion Team | Date: | July 2026
Academic Inst: | Jomo Kenyatta University (JKUAT) | Technical Focus: | Electro-Thermal Sizing & Resistance Optimization

## 1. DOCUMENT SCOPE AND ELECTRO-THERMAL OBJECTIVES

This comprehensive technical document delivers a thorough electro-thermal analysis required to optimize fine Nichrome 80 resistance bridge wires (30 AWG and 32 AWG) for the reliable, remote initiation of custom KNSB-bound pyrogen configurations. In a consolidated pyrogen igniter, the bridge wire serves as the primary thermal transducer. Passing an electric current through this wire converts electrical energy into heat via Joule heating. To achieve immediate initiation of the primary composition (which incorporates elemental sulfur with an auto-ignition threshold of approximately 232°C), the bridge wire should ideally flash to a target temperature of 1000°C (1273.15 K). This extreme over-temperature guarantees immediate, multi-point ignition, eliminating ignition delay and preventing transient chuffing inside the motor casing.

Sizing the bridge wire requires solving the direct mathematical interdependencies between wire gauge, linear resistance, geometric length, source voltage, current drawdown, and thermal response times. This analysis isolates these parameters to provide actionable length, topology, and power recommendations for field-ready battery profiles.

## 2. FOUNDATIONAL MATHEMATICAL GOVERNING EQUATIONS

The electrical and thermodynamic performance of a fine uninsulated wire suspended inside a chemical matrix is governed by Ohm's Law, Joule's First Law, and the fundamental heat equation.

### 2.1. Physical Resistance Modeling

The initial electrical resistance (R) of a round conductor at room temperature depends on its geometric length and cross-sectional area:

R = ρ
e
× (L / A) = ρlinear × L | (Eq. 1)
TECHNICAL REPORT | THE NAKUJA PROJECT | Page 1 of 7

Where L is the active physical length of the wire segment (m), A is the cross-sectional area (π d2 / 4, m

2
), and ρ
e
is the material electrical resistivity. For premium Nichrome 80 (comprising 80% Nickel and 20% Chromium), ρ e
≈ 1.09 × 10-6 Ω·m at room temperature.

### 2.2. Joule Heating and Power Dissipation

When a constant DC voltage source (V) is applied across the isolated bridge wire, the electric current (I) drawn through the circuit is defined by Ohm's Law:

The instantaneous thermal power (P) dissipated as radiant heat across the conductor is defined by Joule's Law:

Equation 3 reveals a critical relationship for design optimization: under constant-voltage conditions, the thermal power output varies inversely with resistance. Shortening the wire decreases its resistance, which exponentially increases the current draw and the total power dissipation.

### 2.3. Thermodynamic Heat Accumulation

To model the transient temperature rise time (t

rise) before full ignition, we evaluate the system as a closed thermodynamic model. Neglecting small localized conductive losses into the surrounding slurry during the initial millisecond phase, the net energy (E) required to elevate the physical wire mass (m) from ambient temperature (Tambient = 20°C) to the target ignition threshold (Ttarget = 1000°C) is expressed as:

Where c
p

is the specific heat capacity of Nichrome 80 (450 J/(kg·K)), ΔT is the net temperature change (1000°C -20°C = 980°C), and m is isolated via the material mass density (ρm

= 8310 kg/m3
) multiplied by wire volume:

The required activation time (t

rise) to achieve immediate thermal breakdown is defined by the ratio of total energy to instantaneous power dissipation:

## 3. COMPREHENSIVE SIZING MATRICES FOR CONDUCTOR PROFILES

The physical and electrical baselines for standard Nichrome 80 wire gauges are defined as:

### 30 AWG Wire: Diameter d = 0.254 mm | Linear Resistance ρ

linear = 21.33 Ω/m

### 32 AWG Wire: Diameter d = 0.203 mm | Linear Resistance ρ

linear = 33.46 Ω/m

I = V / R | (Eq. 2)

P = I²

× R = V²
/ R | (Eq. 3)

E = m × c
p
× ΔT | (Eq. 4)

m = ρm

× A × L | (Eq. 5)

t

rise = E / P = (m × c
p

× ΔT) / (V²
/ R) | (Eq. 6)

•

•

TECHNICAL REPORT | THE NAKUJA PROJECT | Page 2 of 7

3.1. 30 AWG Parametric Performance Table
Length (mm) | Resistance (Ω) | Wire Mass (mg) | Energy to 1000°C (J) | Source Voltage (V) | Current Draw (A) | Power Output (W) | Time to 1000°C (ms)
5.0 mm | 0.1066 | 2.11 | 0.9285 | 3.7 V (1S Li-Ion) | 34.69 A | 128.36 W | 7.23 ms
| | | | 7.4 V (2S Li-Po) | 69.39 A | 513.46 W | 1.81 ms
| | | | 12.0 V (Lead-Acid) | 112.52 A | 1350.21 W | 0.69 ms
| | | | 24.0 V (Bench DAQ) | 225.04 A | 5400.84 W | 0.17 ms
10.0 mm | 0.2133 | 4.21 | 1.8569 | 3.7 V (1S Li-Ion) | 17.35 A | 64.18 W | 28.93 ms
| | | | 7.4 V (2S Li-Po) | 34.69 A | 256.73 W | 7.23 ms
| | | | 12.0 V (Lead-Acid) | 56.26 A | 675.11 W | 2.75 ms
| | | | 24.0 V (Bench DAQ) | 112.52 A | 2700.42 W | 0.69 ms
15.0 mm | 0.3199 | 6.32 | 2.7854 | 3.7 V (1S Li-Ion) | 11.56 A | 42.79 W | 65.10 ms
| | | | 7.4 V (2S Li-Po) | 23.13 A | 171.15 W | 16.27 ms
| | | | 12.0 V (Lead-Acid) | 37.51 A | 450.07 W | 6.19 ms
| | | | 24.0 V (Bench DAQ) | 75.01 A | 1800.28 W | 1.55 ms
TECHNICAL REPORT | THE NAKUJA PROJECT | Page 3 of 7

3.2. 32 AWG Parametric Performance Table
Length (mm) | Resistance (Ω) | Wire Mass (mg) | Energy to 1000°C (J) | Source Voltage (V) | Current Draw (A) | Power Output (W) | Time to 1000°C (ms)
5.0 mm | 0.1673 | 1.34 | 0.5931 | 3.7 V (1S Li-Ion) | 22.12 A | 81.83 W | 7.25 ms
| | | | 7.4 V (2S Li-Po) | 44.23 A | 327.32 W | 1.81 ms
| | | | 12.0 V (Lead-Acid) | 71.73 A | 860.73 W | 0.69 ms
| | | | 24.0 V (Bench DAQ) | 143.45 A | 3442.92 W | 0.17 ms
10.0 mm | 0.3346 | 2.69 | 1.1861 | 3.7 V (1S Li-Ion) | 11.06 A | 40.91 W | 28.99 ms
| | | | 7.4 V (2S Li-Po) | 22.12 A | 163.66 W | 7.25 ms
| | | | 12.0 V (Lead-Acid) | 35.86 A | 430.36 W | 2.76 ms
| | | | 24.0 V (Bench DAQ) | 71.73 A | 1721.46 W | 0.69 ms
15.0 mm | 0.5019 | 4.03 | 1.7792 | 3.7 V (1S Li-Ion) | 7.37 A | 27.28 W | 65.23 ms
| | | | 7.4 V (2S Li-Po) | 14.74 A | 109.11 W | 16.31 ms
| | | | 12.0 V (Lead-Acid) | 23.91 A | 286.91 W | 6.20 ms
| | | | 24.0 V (Bench DAQ) | 47.82 A | 1147.64 W | 1.55 ms

## 4. ANALYSIS OF ELECTRICAL CONSUMPTION LIMITATIONS

### 4.1. Source Internal Resistance & Voltage Sag

A critical challenge in igniter implementation is assuming the power supply can deliver infinite current. Every battery possesses a distinct internal resistance (Rint). When the bridge wire loop is closed, the true terminal voltage (Vterminal) available to the igniter drops due to internal dissipation:

Vterminal = Vopen_circuit - (I × Rint) | (Eq. 7)
TECHNICAL REPORT | THE NAKUJA PROJECT | Page 4 of 7

Standard consumer 9V alkaline transistor batteries are entirely unsuitable for this application due to their exceptionally high internal resistance (Rint ≈ 1–2 Ω). Attempting to draw more than 2 Amperes causes the terminal voltage to collapse instantly to near 0V, leading to an ignition hangfire. Operators must utilize lowimpedance power sources, such as Lithium-Polymer (Li-Po) battery packs with a minimum continuous discharge rating of 30C, or heavy-duty sealed lead-acid field batteries.

### 4.2. Parasitic Resistance Along Field Lead Wires

Because static test firings must be commanded from a safe remote radius (minimum 30 to 50 meters away for validation), the copper extension wire introduces significant parasitic resistance (Rlead). Standard 24 AWG copper phone wire has a round-trip linear resistance of approximately 0.168 Ω per 10 meters. For a 30-meter safety line, this adds 0.50 Ω of parasitic resistance to the firing loop, which alters circuit behavior.

## 5. ELECTRO-THERMAL ANALYSIS OF MULTI-WIRE CONDUCTOR CONFIGURATIONS

When optimizing high-impulse ignition infrastructure, propulsion teams occasionally consider increasing the number of active Nichrome bridge wires within a single pyrogen core to gain redundancy or to expand the initial localized flame front area. However, from an electrical and thermodynamic standpoint, adding two or more Nichrome wires introduces complex consequences that can compromise the ignition transient unless power delivery is heavily scaled to compensate.

### 5.1. Mathematical Analysis of Multiple Wire Typologies

To evaluate the electrical impact of introducing a second identical Nichrome 80 bridge wire, we assume a verified baseline wire profile: 32 AWG, 10.0 mm length, cold resistance R = 0.3346 Ω. When adding a second wire (n = 2), the circuit must conform to either a Series or Parallel topology.

### 5.1.1. TYPOLOGY A: SERIES CONFIGURATION (N = 2)

In a series arrangement, the total resistance of the bridge wire system increases linearly with the number of wires (n):

Under a constant voltage source (V = 7.4 V from a 2S Li-Po battery), the total circuit current drops:

The total power dissipated across the entire circuit decreases significantly, and the power allocated to each individual wire segment (Pwire) scales down sharply by a factor of n

2
:
Rtotal = n × R = 2 × 0.3346 Ω = 0.6692 Ω | (Eq. 8)

I

total = V / Rtotal = 7.4 V / 0.6692 Ω = 11.06 A | (Eq. 9)

Pwire = Itotal

2

× R = (11.06 A)²
× 0.3346 Ω = 40.92 W | (Eq. 10)
TECHNICAL REPORT | THE NAKUJA PROJECT | Page 5 of 7

Thermodynamic Impact: Splitting the energy in series drops individual wire power from 163.66 W to 40.92 W, lengthening the thermal rise time to 28.99 ms. Series wiring slows down the initiation transient, increasing overall ignition lag.

### 5.1.2. TYPOLOGY B: PARALLEL CONFIGURATION (N = 2)

In a parallel arrangement, clustered directly at the pyrogen bead, the total equivalent resistance drops by half:

Assuming an ideal power supply that can maintain a constant terminal voltage (V = 7.4 V), the total current draw doubles to 44.23 A, allowing each wire to maintain its full power draw. However, this ideal scenario is constrained by field-line variables.

### 5.2. The Parasitic Line Resistance Bottleneck (Real-World Constraints)

The mathematical advantage of a parallel configuration breaks down when factoring in real-world field conditions. Real-world field operations involve line drop across the extension safety cables (Rlead = 0.50 Ω):

Scenario 1 (Single Wire with Field Leads): Total resistance is 0.3346 Ω + 0.50 Ω = 0.8346 Ω. The current draw is 8.87 A, delivering 26.32 W of thermal power to the active wire element.

Scenario 2 (Two Parallel Wires with Field Leads): Total equivalent loop resistance is 0.1673 Ω + 0.50 Ω = 0.6673 Ω. Loop current is 11.09 A. Total power split across the cluster is 20.58 W, yielding only 10.29 W per wire segment.

Due to the voltage drop across long field leads, adding a second wire in parallel reduces the actual power delivered to each active wire segment from 26.32 W down to 10.29 W. This drop in heat flux slows down thermal activation significantly.

### 5.3. Internal Ballistics & Thermodynamic Effects

Thermal Boundary Layer Collapse: A single, highly optimized 32 AWG wire provides a concentrated point source of energy. When wrapped tightly into a small pyrogen bead, it efficiently creates a localized pocket of high-pressure gas. Spreading this energy across multiple wires lowers the peak temperature at any single point if the power source sags, making it harder to cross the critical auto-ignition threshold.

Asynchronous Thermal Rupture: In a parallel cluster, minor differences in wire length, contact resistance, or local density mean one wire will always reach ignition temperature slightly ahead of the other. The moment the primary composition ignites around the faster wire, the resulting flame front melts or breaks the neighboring wire loop, rendering the second wire redundant.

CATASTROPHIC HANGFIRE HAZARD: PARALLEL PERFORMANCE PENALTIES

Attempting to split power across parallel elements over long field lines causes a severe drop in localized heat flux. Conductor redundancy without an isolated, independent dual-channel power source results in a slower, cooler burn sequence that degrades motor start reliability.

Rtotal = R / n = 0.3346 Ω / 2 = 0.1673 Ω | (Eq. 11)

•

•

1.

2.

TECHNICAL REPORT | THE NAKUJA PROJECT | Page 6 of 7

## 6. ACTIONABLE DESIGN OPTIMIZATION AND ENGINEERING RECOMMENDATIONS

Based on the electro-thermal values derived across this combined analysis, the following design standards are established for the project's propulsion testing:

Optimal Gauge and Length Selection: Standardize on a single 32 AWG Nichrome 80 wire cut to an active length of 10.0 mm. This geometry yields a reliable cold resistance of 0.3346 Ω, requiring a minimal thermal energy accumulation of only 1.1861 Joules to reach the 1000°C threshold.

Power Source Calibration: The minimal acceptable field power supply is a 7.4V Lithium-Polymer (2S Li-Po) battery pack with a high C-rating. When connected to a 10.0 mm, 32 AWG bridge wire, this configuration draws 22.12 Amperes, generating an instantaneous thermal power burst of 163.66 Watts. This configuration heats the wire to the target temperature in just 7.25 milliseconds, guaranteeing immediate, reliable pyrogen ignition.

Redundancy Protocol: For the scale of pyrogen systems utilized in M-class motors, adding two or more Nichrome wires within the same loop is unnecessary and highly discouraged. If structural redundancy is required to mitigate handling risks during field setup, operators must deploy two entirely separate, isolated igniter systems running on independent power loops. This approach delivers true backup capability without compromising the electrical and thermal efficiency of the primary circuit.

## 7. REFERENCES

ASTM B344, Standard Specification for Drawn or Rolled Nickel-Chromium and Nickel-Chromium-Iron Alloys for Electrical Heating Elements, ASTM International.

NASA SP-8051, Solid Rocket Motor Igniters, National Aeronautics and Space Administration Design Criteria Monograph.

Ohm, G. S., The Galvanic Circuit Investigated Mathematically, Historical Propulsion Systems Foundations.

1.

2.

3.

•

•

•

TECHNICAL REPORT | THE NAKUJA PROJECT | Page 7 of 7
