nakujaproject/Internship-2026/01_SOLID_PROPULSION/01_Propellant/Liners/Liner_Preparation.jpeg

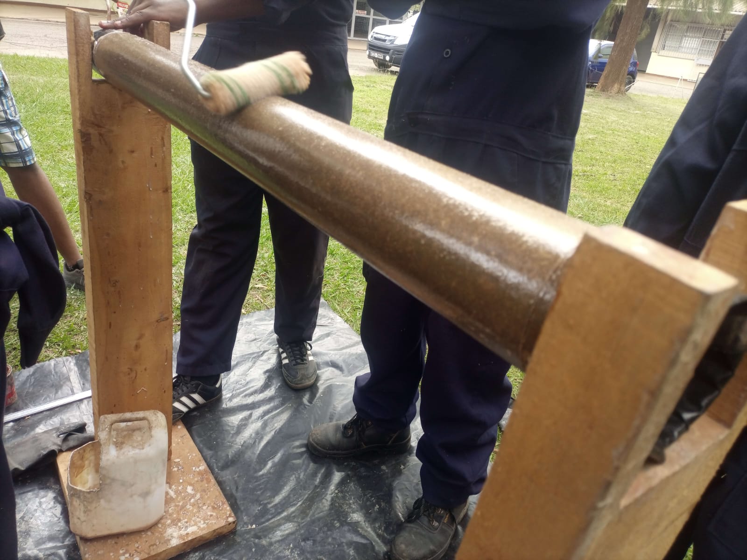
01_SOLID_PROPULSION/01_Propellant/Liners/Liner_Preparation.jpeg
