nakujaproject/Internship-2026/01_SOLID_PROPULSION/03_Ignition_Circuit/Software/Web_Dashboard/screenshots/dashboard_home_v1.png

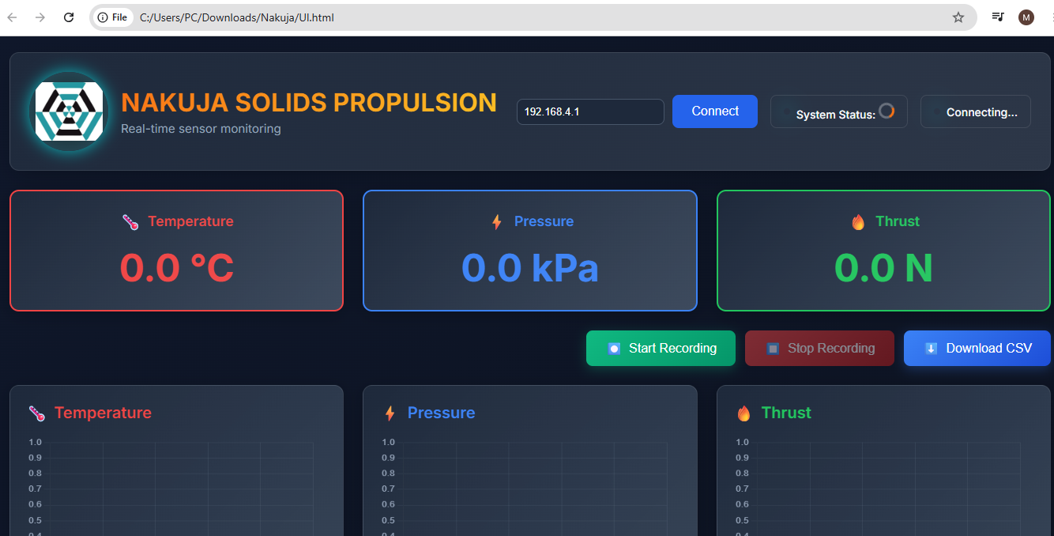
01_SOLID_PROPULSION/03_Ignition_Circuit/Software/Web_Dashboard/screenshots/dashboard_home_v1.png
