nakujaproject/Internship-2026/01_SOLID_PROPULSION/Static_Tests/One_Grain_Tests/Static_test_#7 Suppressant(repeat)/Thrust curve comparison (Simulated vs Actual vs Suppressed).jpeg

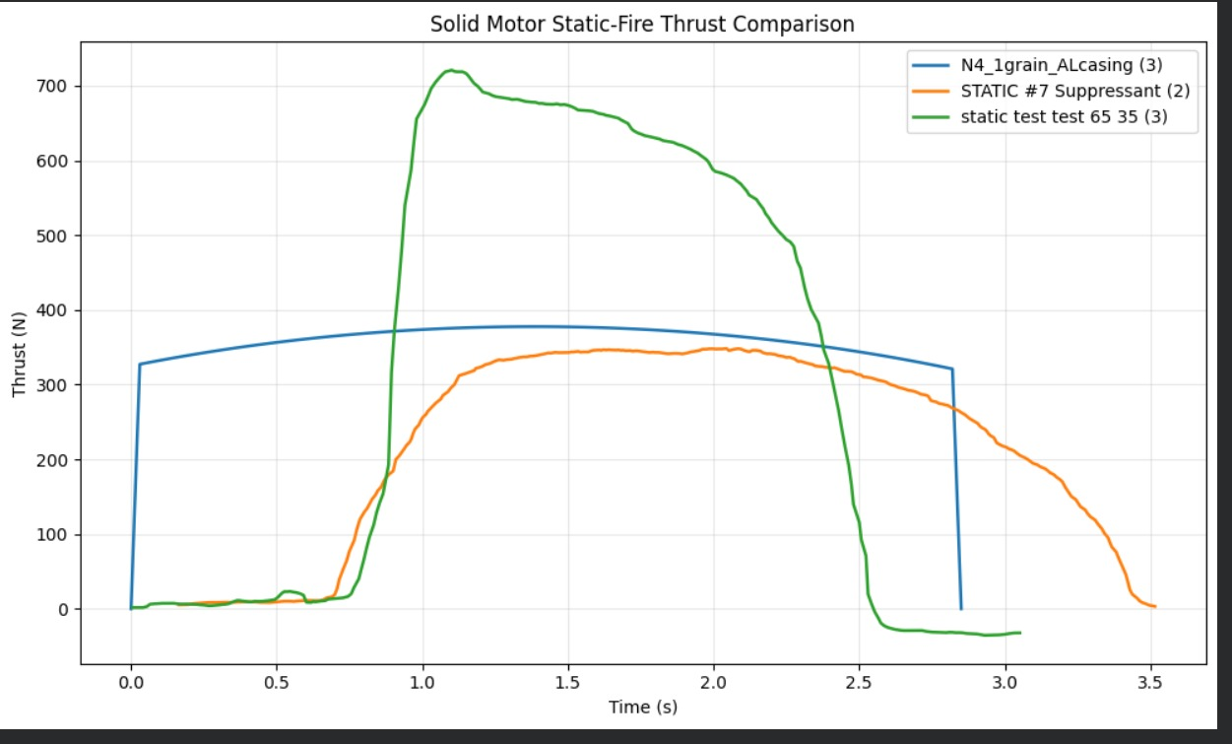
01_SOLID_PROPULSION/Static_Tests/One_Grain_Tests/Static_test_#7 Suppressant(repeat)/Thrust curve comparison (Simulated vs Actual vs Suppressed).jpeg
