nakujaproject/Internship-2026/01_SOLID_PROPULSION/Static_Tests/Three_Grain_Test/Quantitative results.jpeg

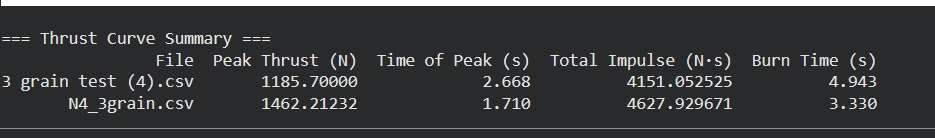
01_SOLID_PROPULSION/Static_Tests/Three_Grain_Test/Quantitative results.jpeg
