nakujaproject/Internship-2026/01_SOLID_PROPULSION/02_Machining/one-grain static test motor/bulkHead_94mm.pdf

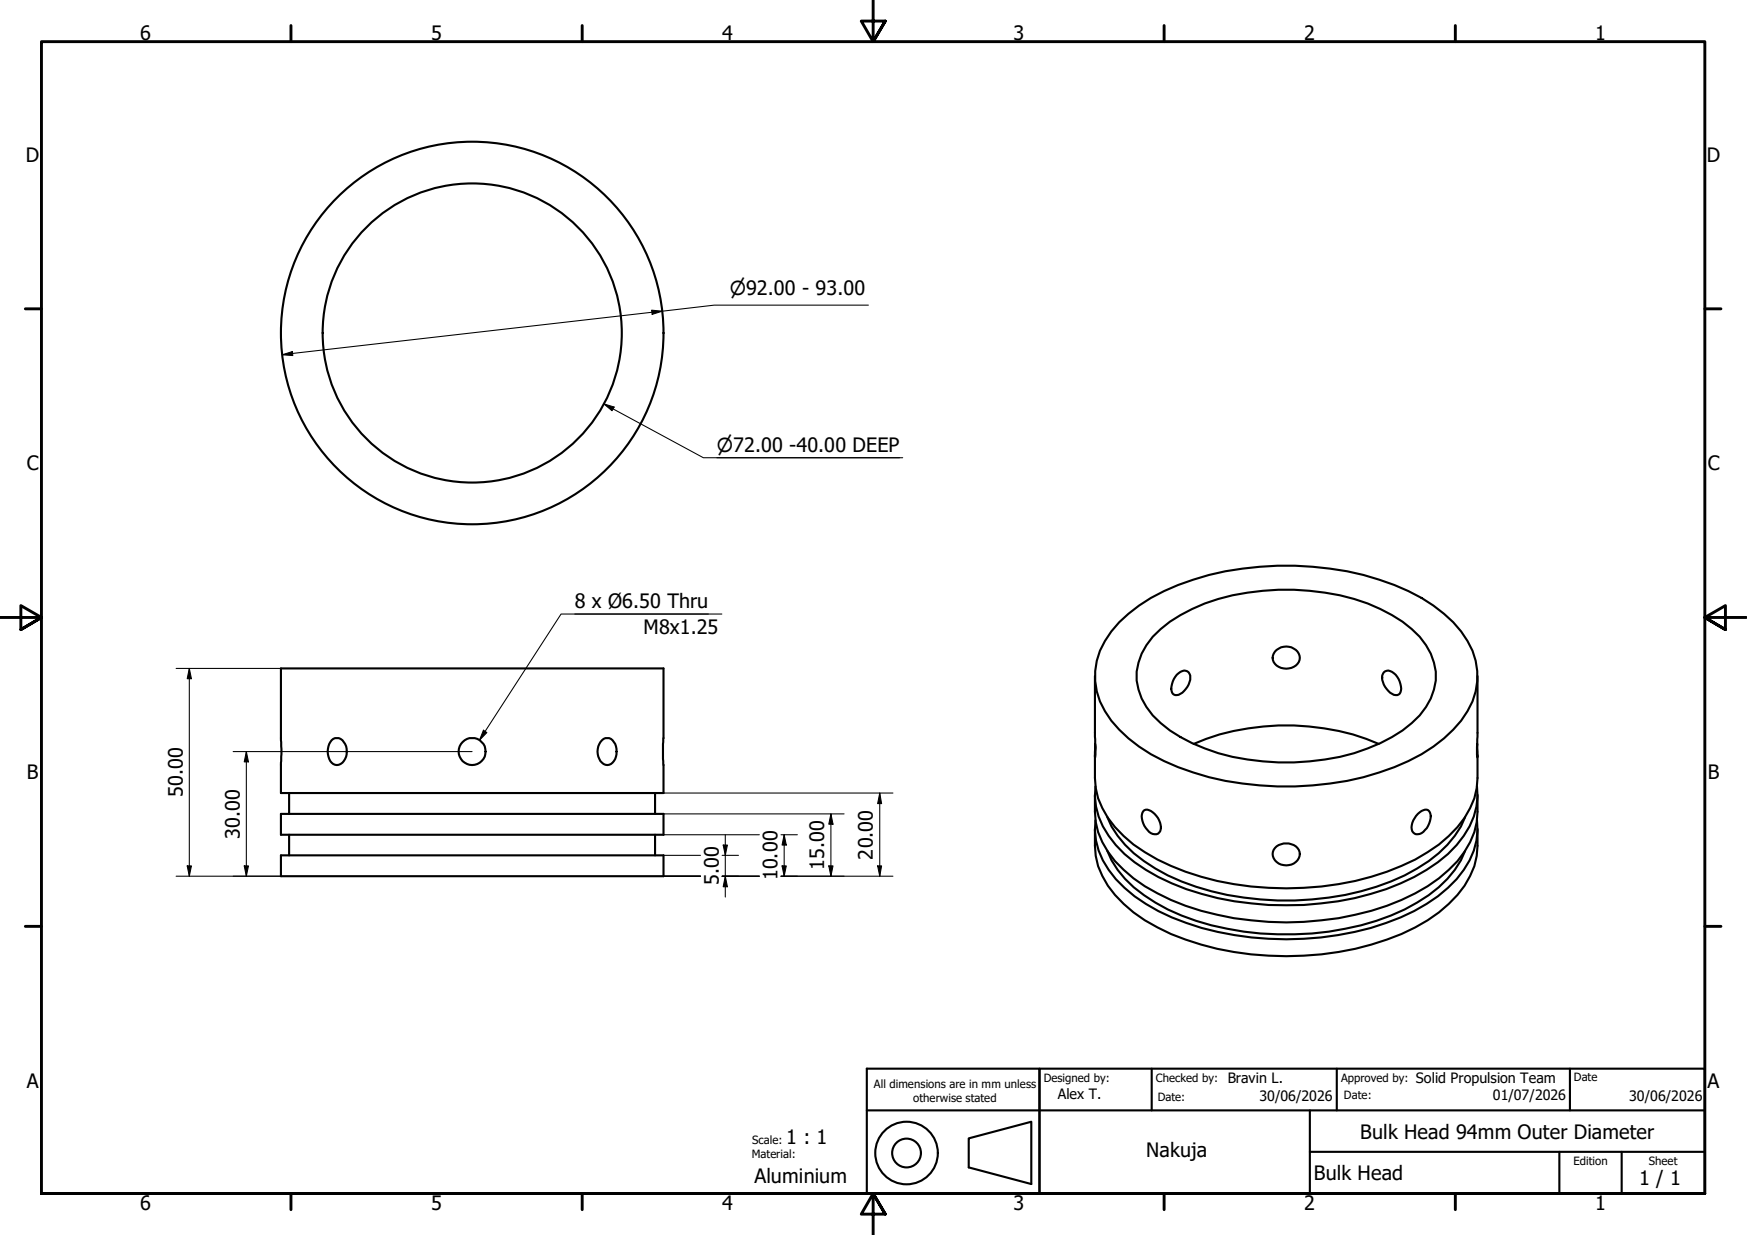
[picture p140: page 1]
⌀72.00 -40.00 DEEP; 8 x Ø6.50 Thru; Scale: 1 : 1

All dimensions are in mm unless otherwise stated | Designed by: Alex T. | Checked by: Bravin L. Date: 30/06/2026 | Approved by: Solid Propulsion Team Date: 01/07/2026 | Date 30/06/2026

Nakuja | Bulk Head 94mm Outer Diameter

Bulk Head | Edition | Sheet 1 / 1
