nakujaproject/Internship-2026/01_SOLID_PROPULSION/02_Machining/one-grain static test motor/casing_258mm.pdf

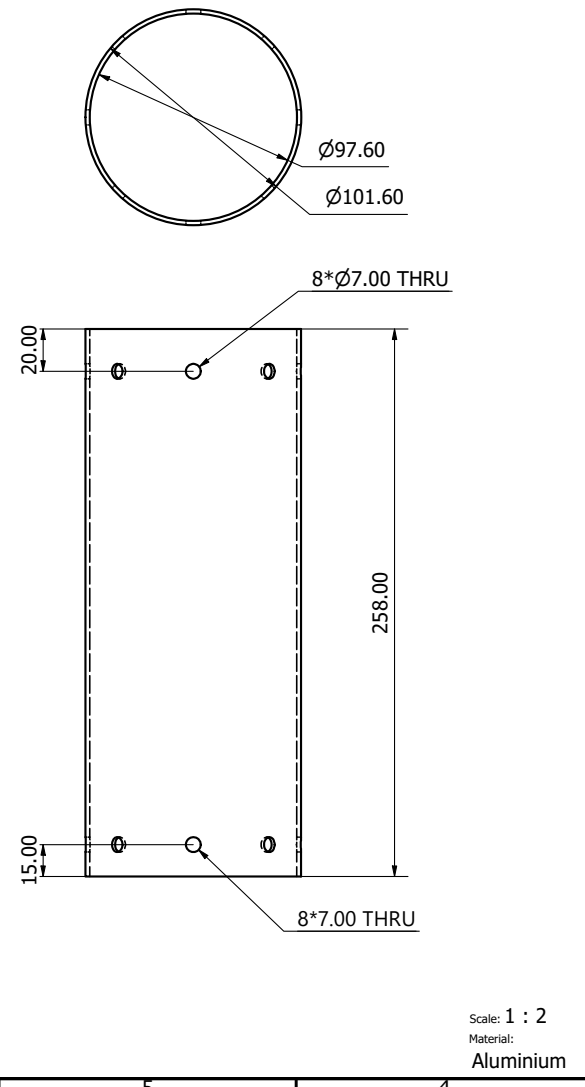
[picture p141: page 1]
Scale: 1 : 2; 8*⌀7.00 THRU; 8*7.00 THRU

All dimensions are in mm unless otherwise stated | Designed by: Alex T. | Checked by: Bravin L. Date: 29/06/2026 | Approved by: Solid Propulsion Team Date: 29/06/2026 | Date 29/06/2026

Nakuja Project | Single 145mm-Grain Casing

casing_258mm_long | Edition | Sheet 1 / 1
