nakujaproject/Internship-2026/01_SOLID_PROPULSION/02_Machining/one-grain static test motor/nozzle_94mm.pdf

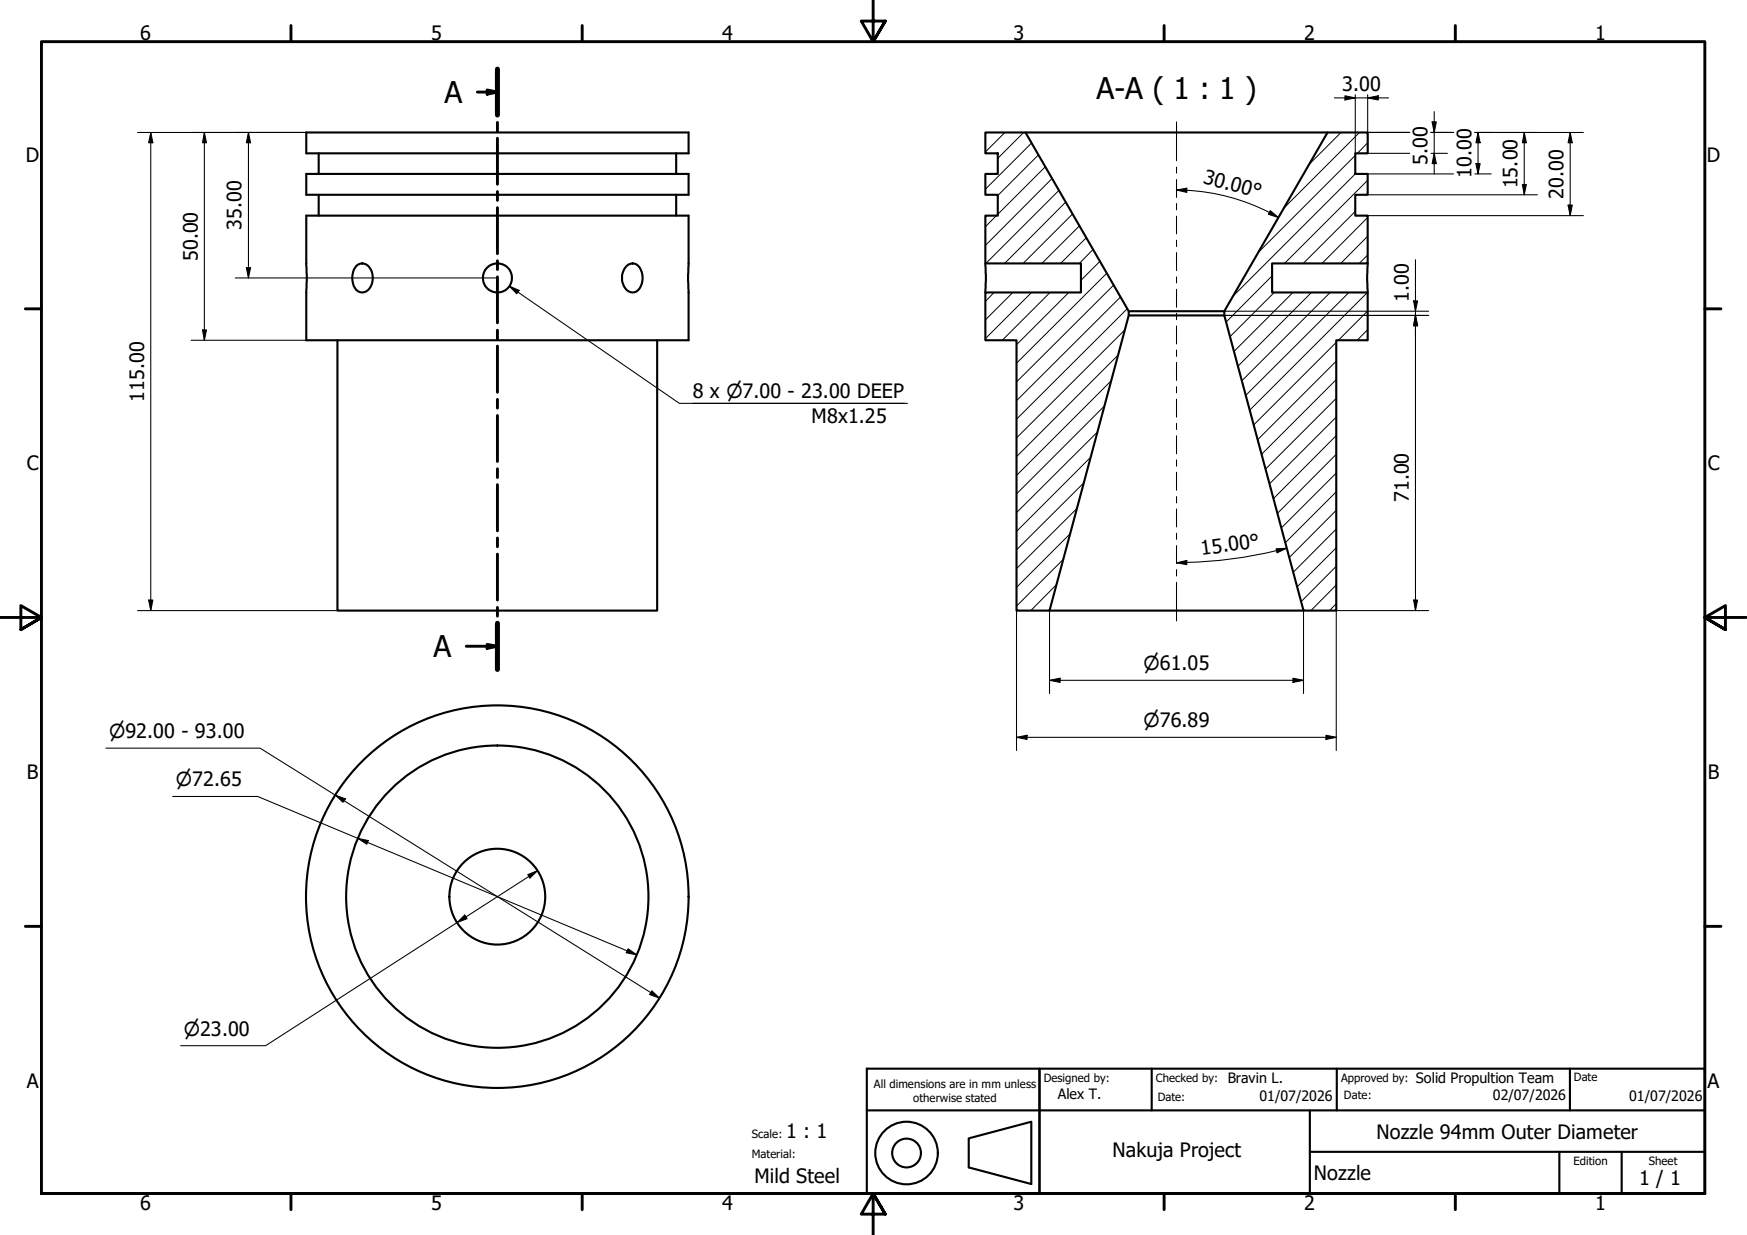
[picture p142: page 1]
Mild Steel; 8 x ⌀7.00 - 23.00 DEEP; Scale: 1 : 1

All dimensions are in mm unless otherwise stated | Designed by: Alex T. | Checked by: Bravin L. Date: 01/07/2026 | Approved by: Solid Propultion Team Date: 02/07/2026 | Date 01/07/2026

Nakuja Project | Nozzle 94mm Outer Diameter

Nozzle | Edition | Sheet 1 / 1
