nakujaproject/Internship-2026/01_SOLID_PROPULSION/04_3D_Printing/Casting_tools/Core_rod_new.pdf

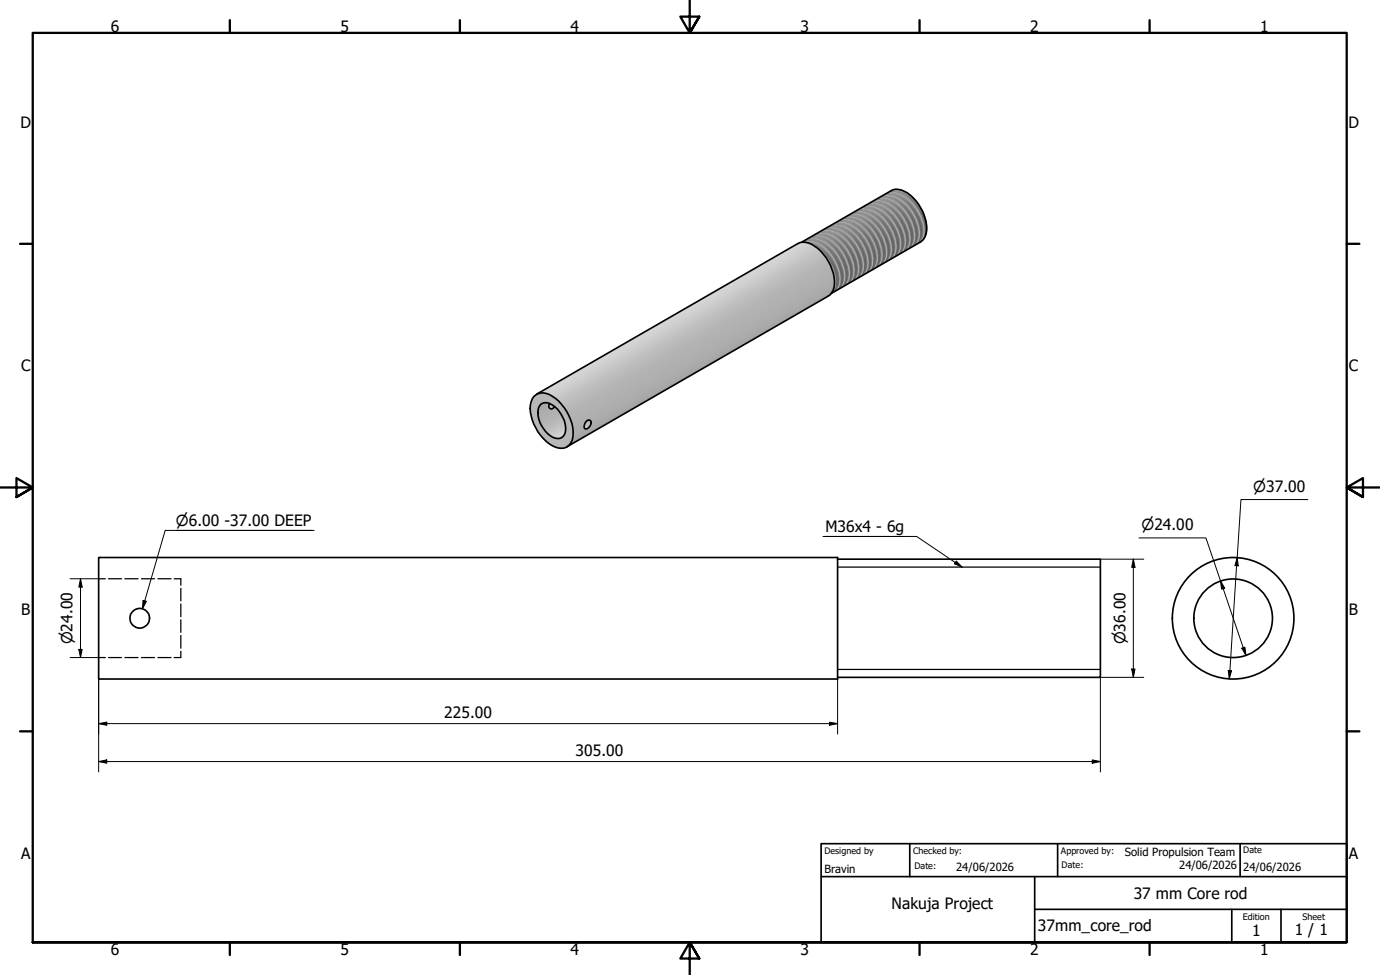
[picture p143: page 1]
⌀6.00 -37.00 DEEP

Designed by Bravin | Checked by: Date: 24/06/2026 | Approved by: Solid Propulsion Team Date: 24/06/2026 | Date 24/06/2026

Nakuja Project | 37 mm Core rod

37mm_core_rod | Edition 1 | Sheet 1 / 1
