nakujaproject/Internship-2026/01_SOLID_PROPULSION/04_3D_Printing/Casting_tools/BasePlate_37x86_Drawing.pdf

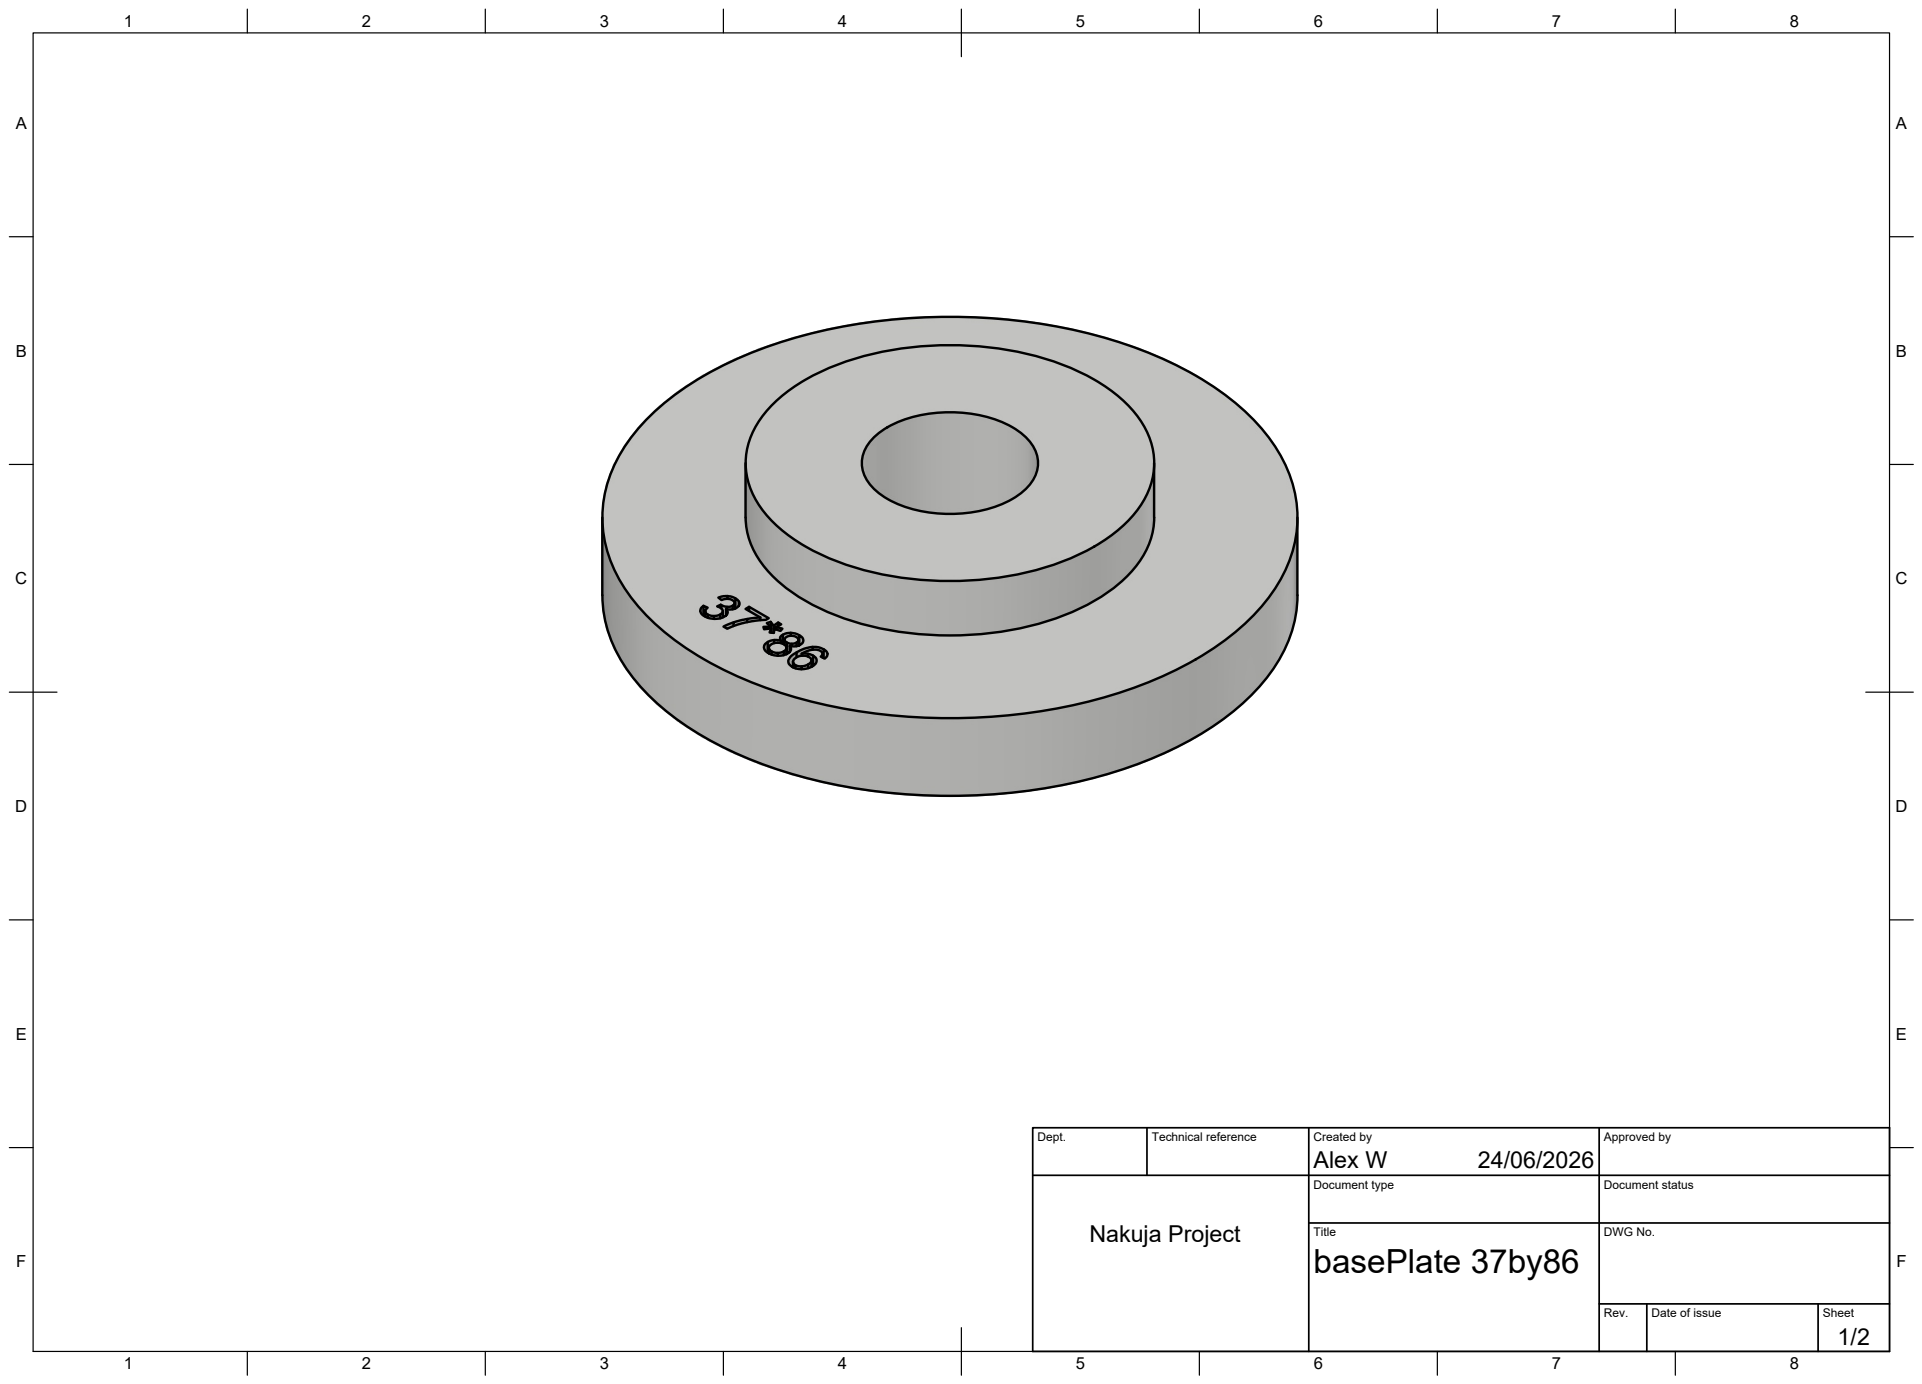
[picture p145: page 1]
Title; DWG No.; Rev.; Date of issue; Sheet; Nakuja Project; basePlate 37by86

Dept. | Technical reference | Created by Alex W 24/06/2026 | Approved by

Document type | Document status

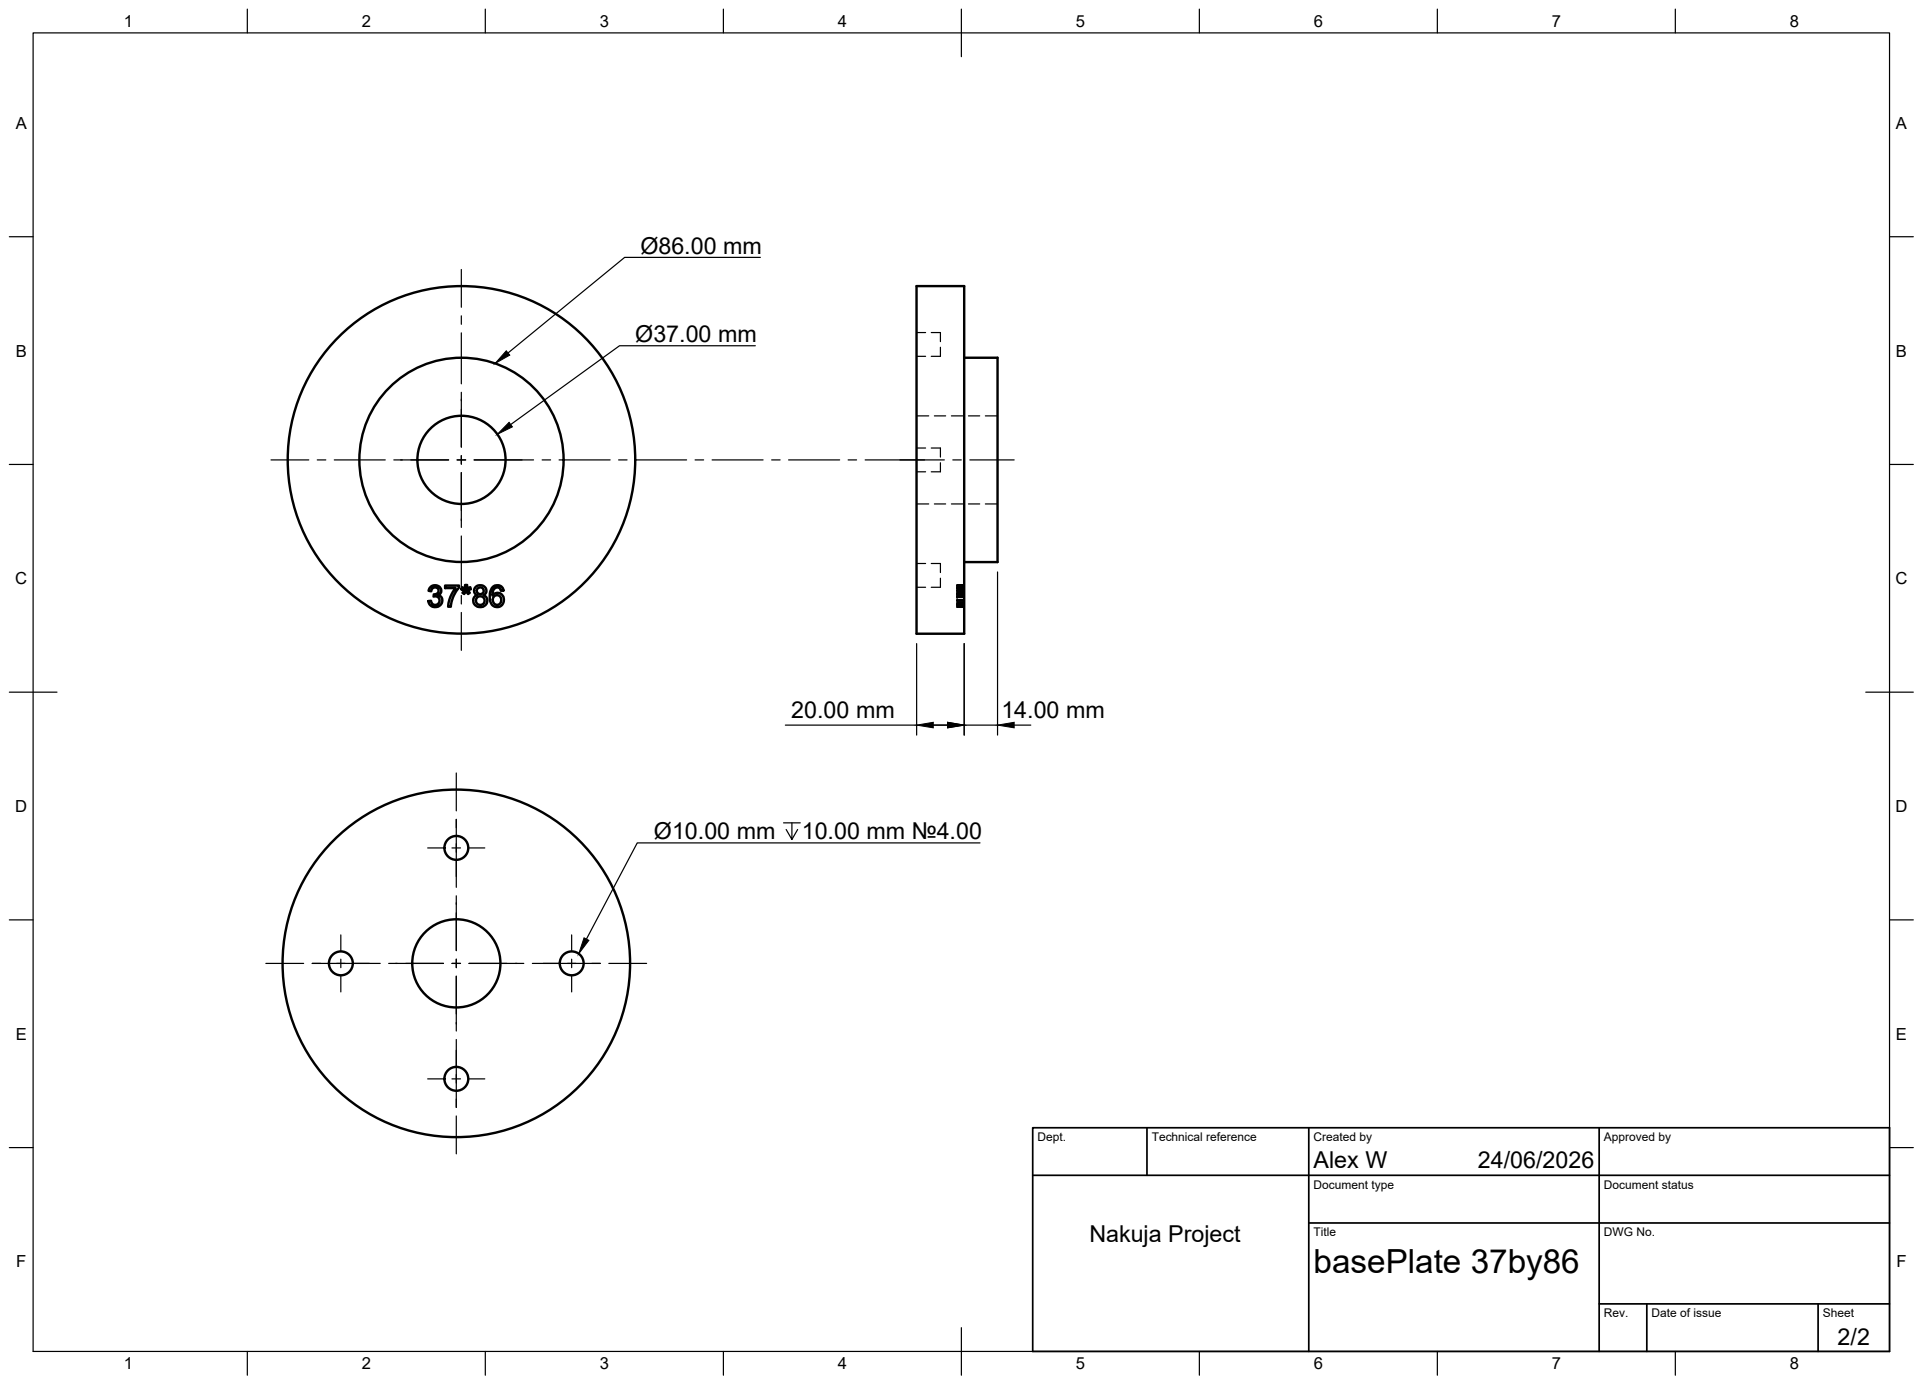
[picture p146: page 2]
Title; DWG No.; Rev.; Date of issue; Sheet; Nakuja Project; basePlate 37by86

Dept. | Technical reference | Created by Alex W 24/06/2026 | Approved by

Document type | Document status
